seawarrior181/PasswordPump_II/3D-Print/Jimmys_Design/PXL_20210318_081315096.jpg

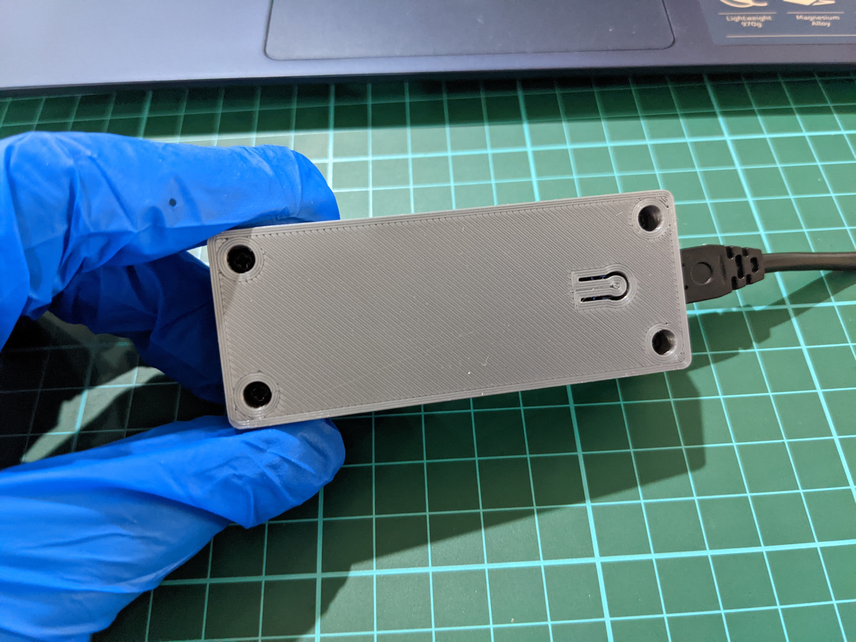
3D-Print/Jimmys_Design/PXL_20210318_081315096.jpg
