seawarrior181/PasswordPump_II/3D-Print/scootercommuter_Design/EncoderModel/PPBox_1.jpg

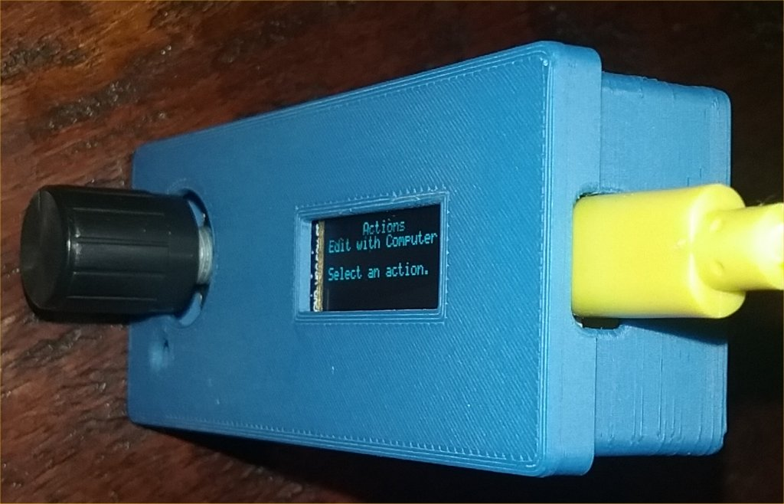
3D-Print/scootercommuter_Design/EncoderModel/PPBox_1.jpg
