seawarrior181/PasswordPump_II/3D-Print/scootercommuter_Design/EncoderModel/PPBox_2.jpg

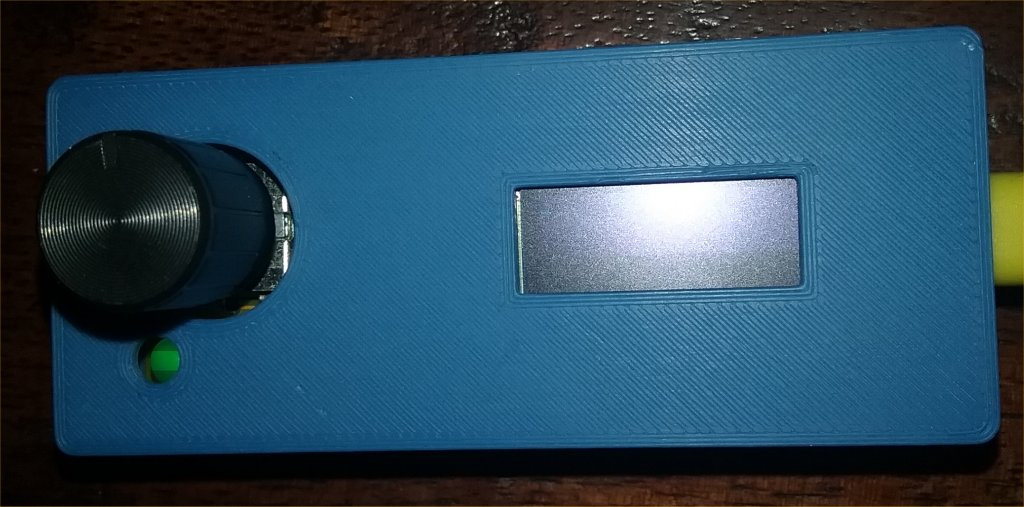
3D-Print/scootercommuter_Design/EncoderModel/PPBox_2.jpg
