seawarrior181/PasswordPump_II/media/20200301_110927.jpg

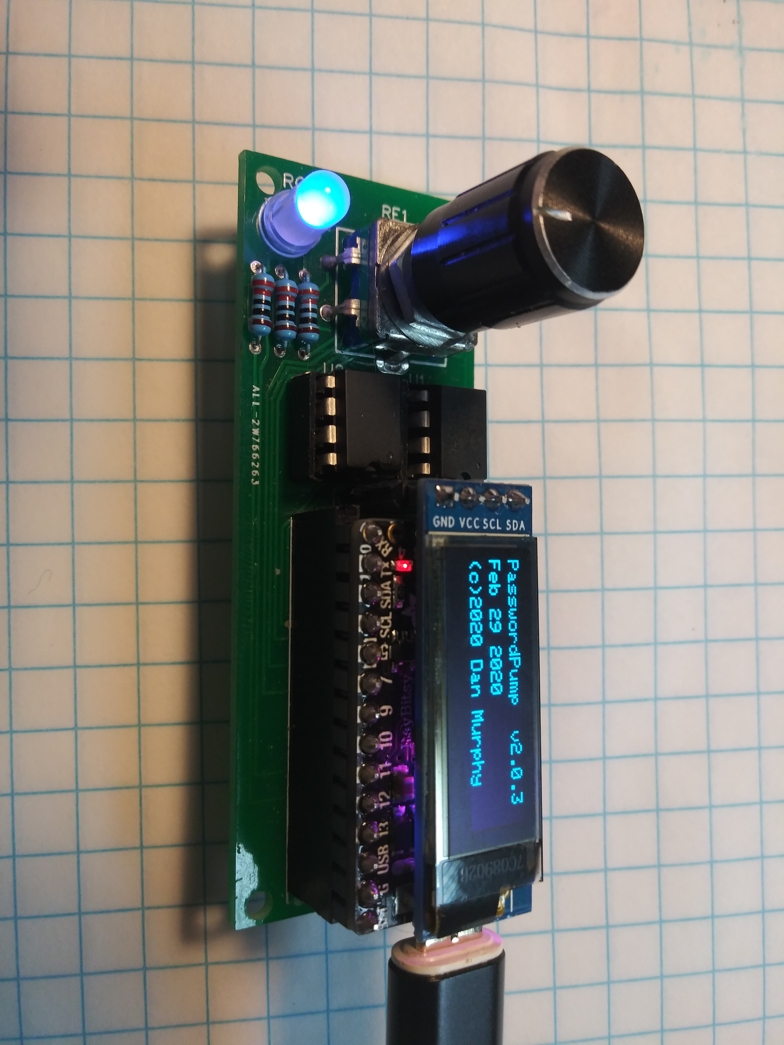
media/20200301_110927.jpg
