seawarrior181/PasswordPump_II/media/20200301_113238.jpg

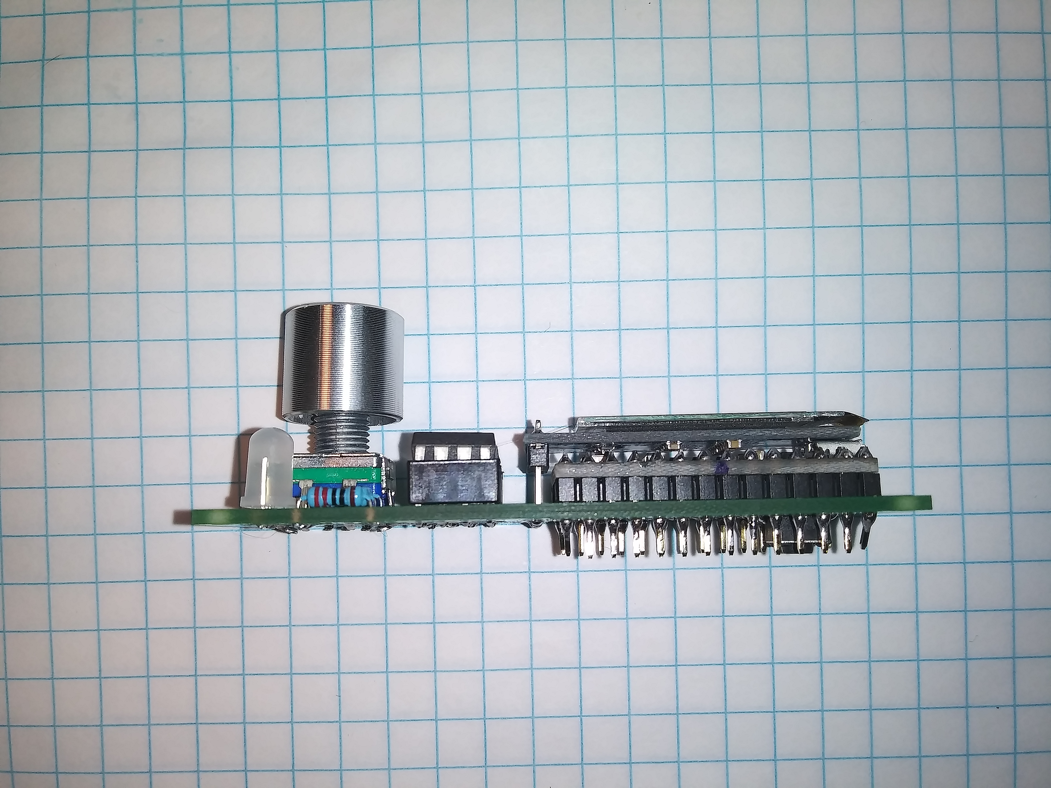
media/20200301_113238.jpg
