seawarrior181/PasswordPump_II/media/20200301_124309.jpg

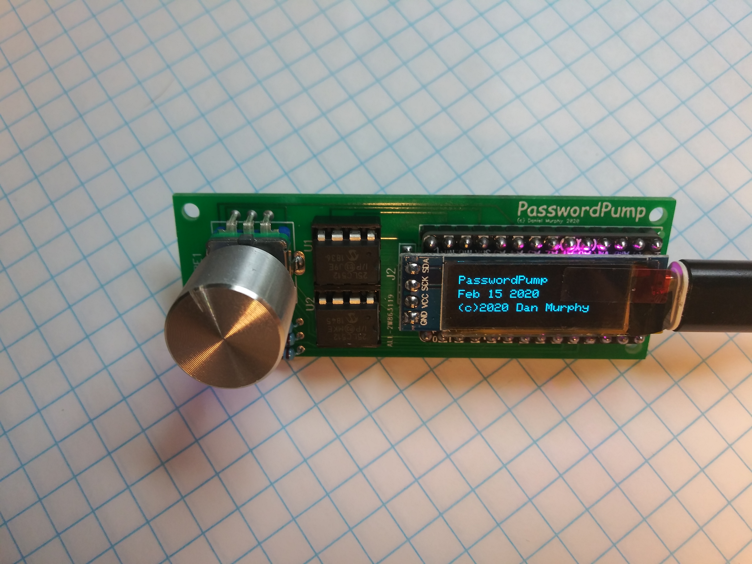
media/20200301_124309.jpg
