seawarrior181/PasswordPump_II/media/20200301_130727.jpg

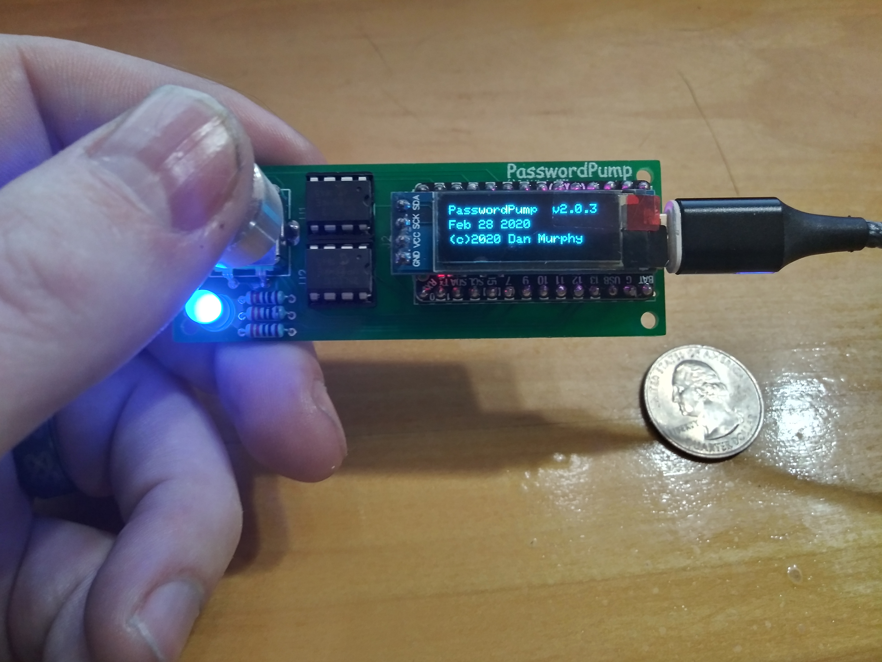
media/20200301_130727.jpg
