seawarrior181/PasswordPump_II/media/20201129_113634_HDR.jpg

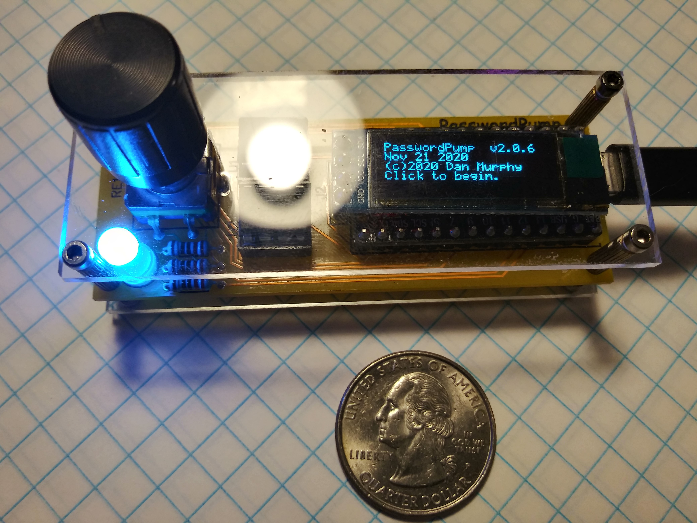
media/20201129_113634_HDR.jpg
