seawarrior181/PasswordPump_II/media/20210111_080319_HDR.jpg

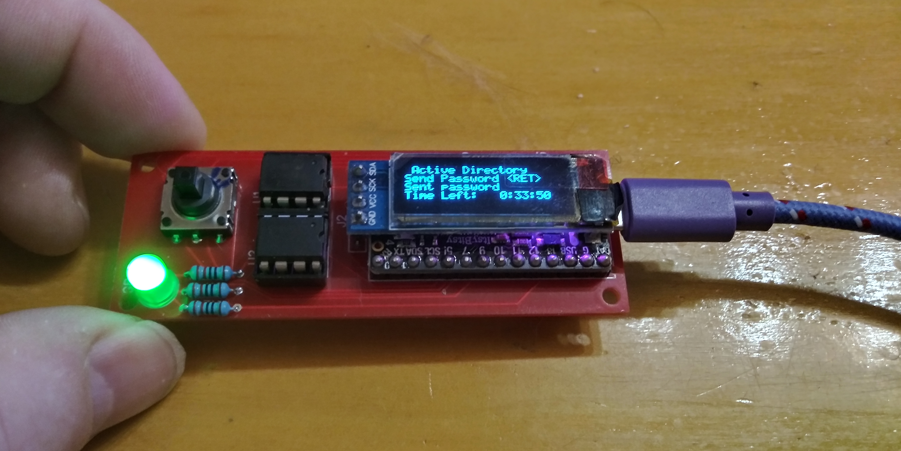
media/20210111_080319_HDR.jpg
