seawarrior181/PasswordPump_II/media/20210115_154211.jpg

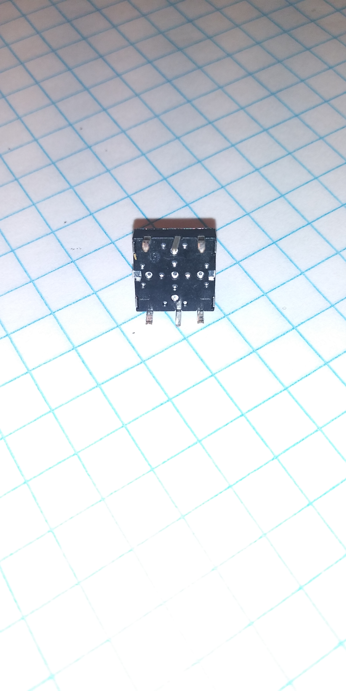
media/20210115_154211.jpg
