seawarrior181/PasswordPump_II/media/20210116_133526.jpg

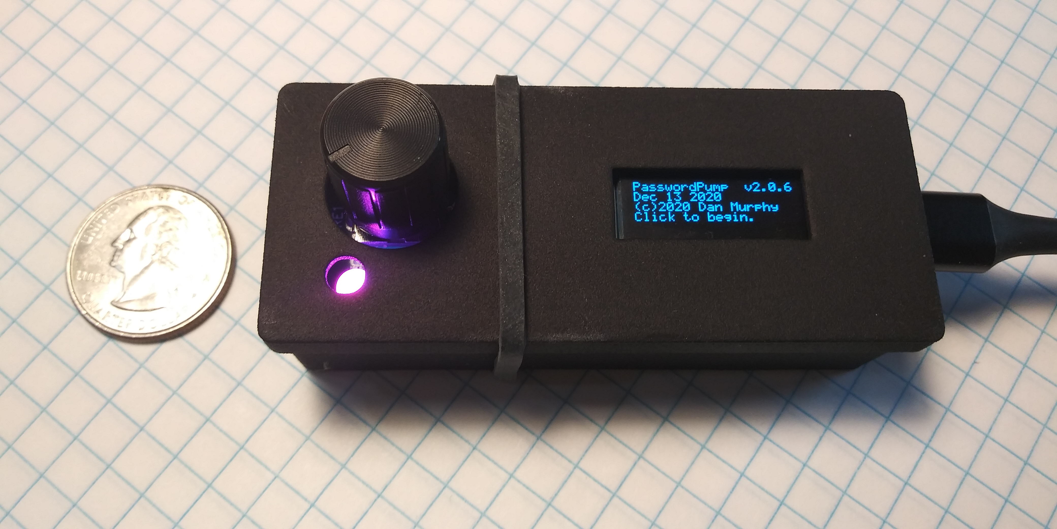
media/20210116_133526.jpg
