seawarrior181/PasswordPump_II/media/20210118_093656.jpg

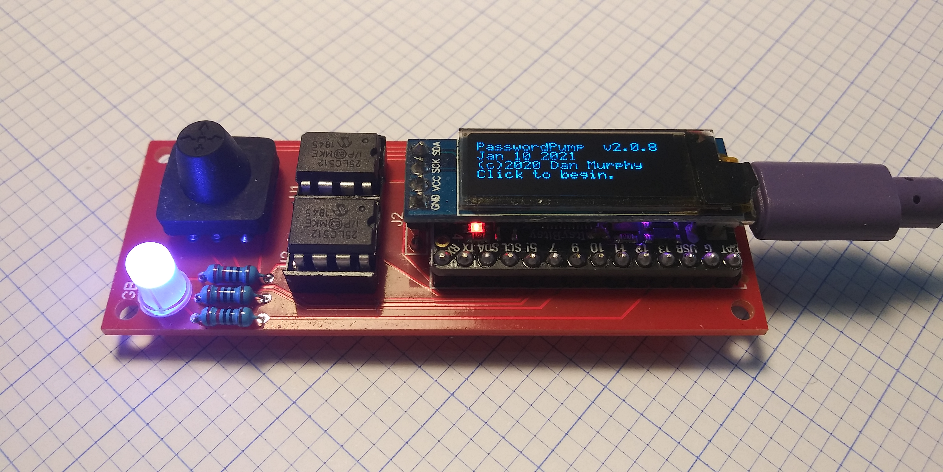
media/20210118_093656.jpg
