seawarrior181/PasswordPump_II/media/20210210_074406.jpg

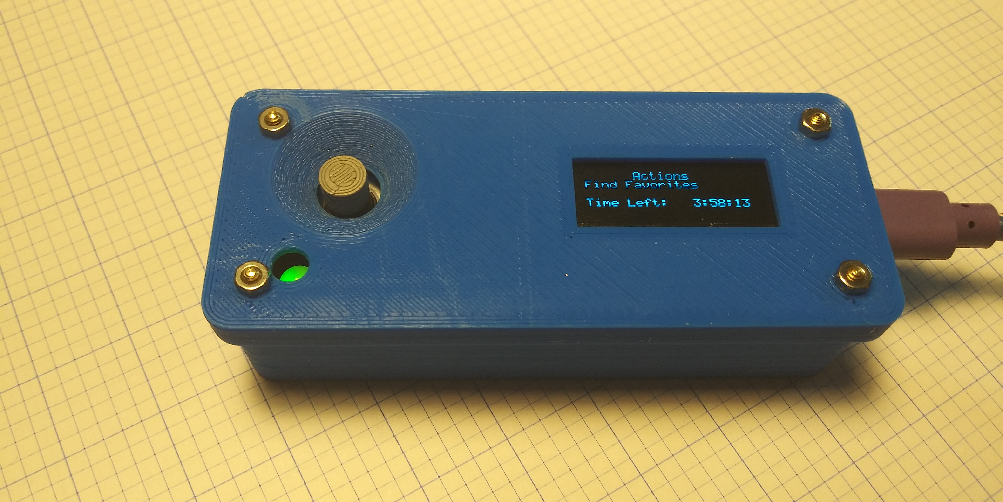
media/20210210_074406.jpg
