seawarrior181/PasswordPump_II/media/20210212_081341.jpg

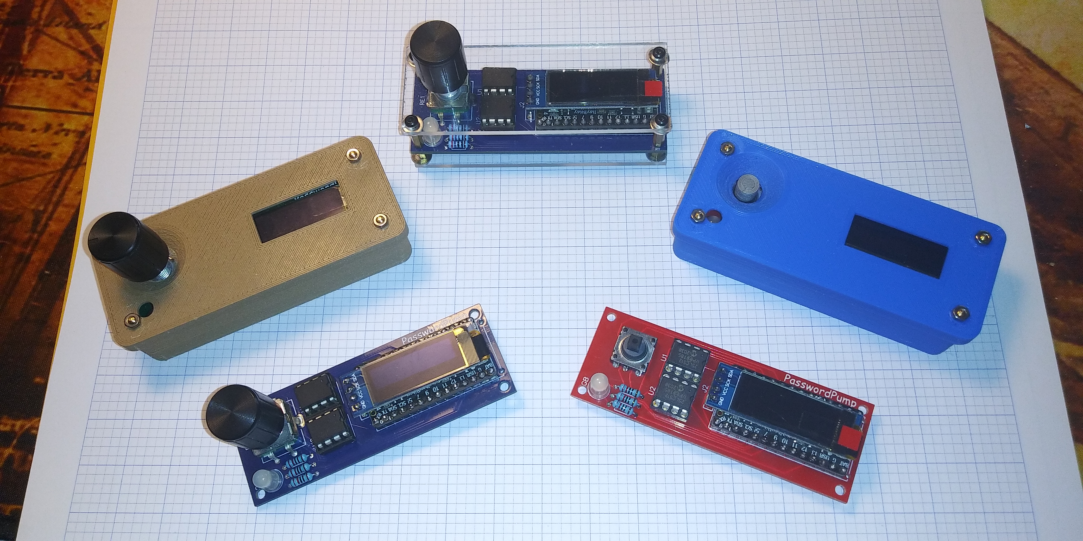
media/20210212_081341.jpg
