seawarrior181/PasswordPump_II/media/20210212_084028.jpg

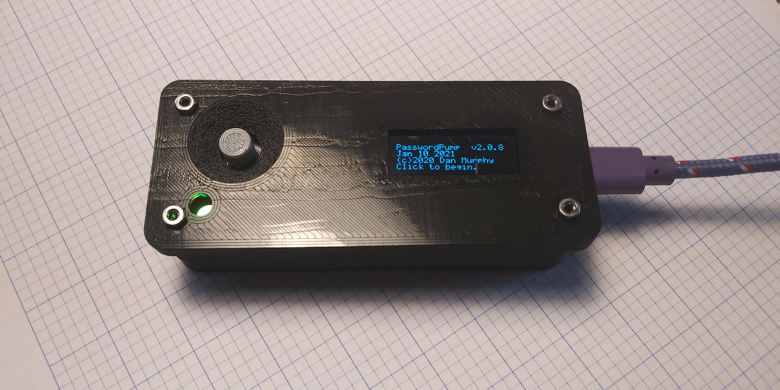
media/20210212_084028.jpg
