seawarrior181/PasswordPump_II/media/20210410_101105.jpg

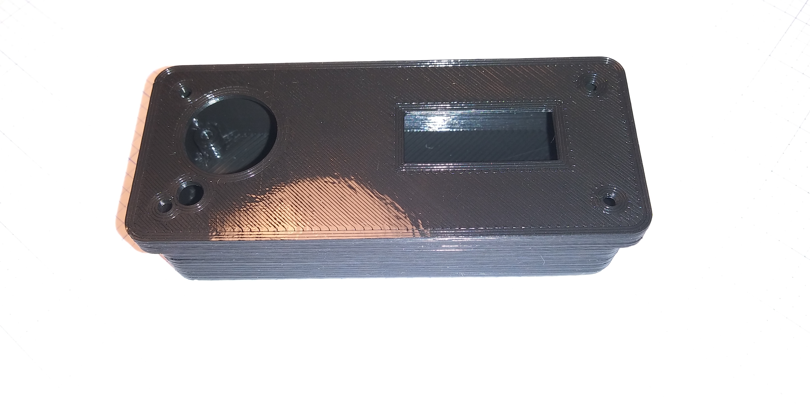
media/20210410_101105.jpg
