seawarrior181/PasswordPump_II/media/DriverUpdated.jpg

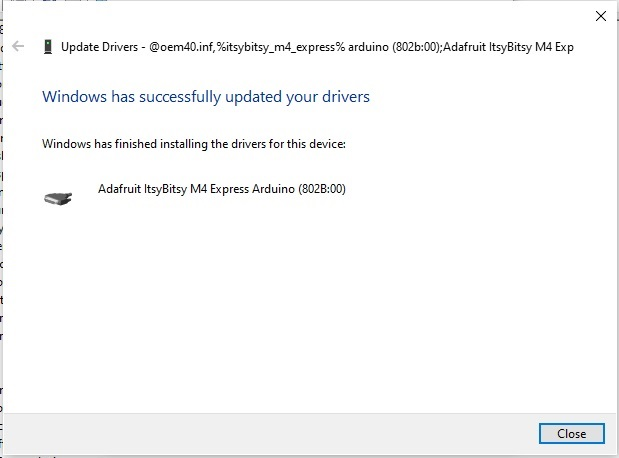
media/DriverUpdated.jpg
