seawarrior181/PasswordPump_II/media/DriverUpdated_2.jpg

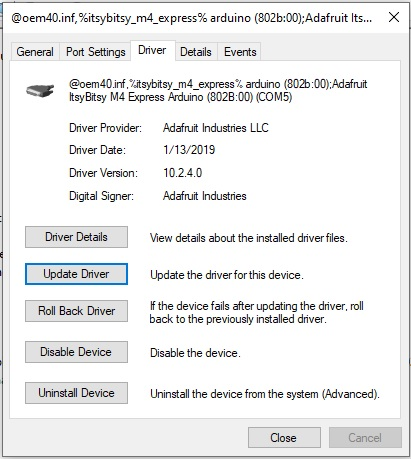
media/DriverUpdated_2.jpg
