seawarrior181/PasswordPump_II/media/FritzingBreadboard.jpg

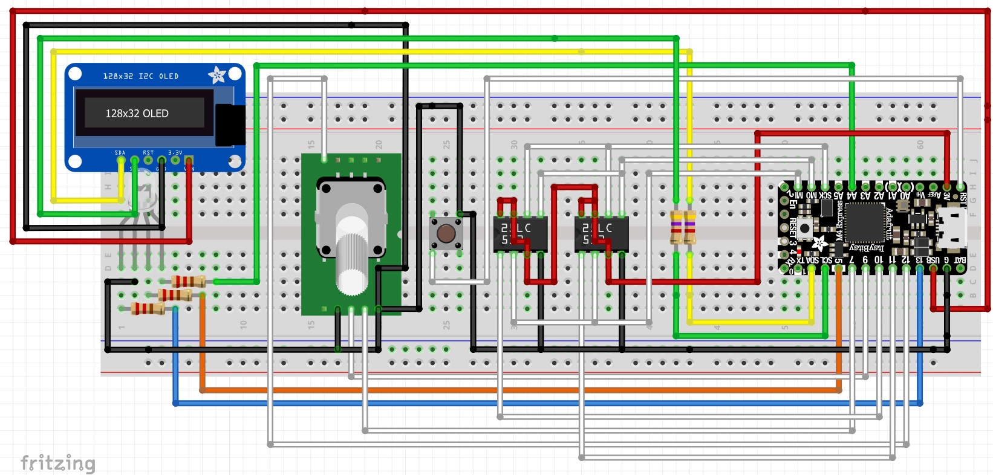
media/FritzingBreadboard.jpg
