seawarrior181/PasswordPump_II/media/JoystickGround.jpg

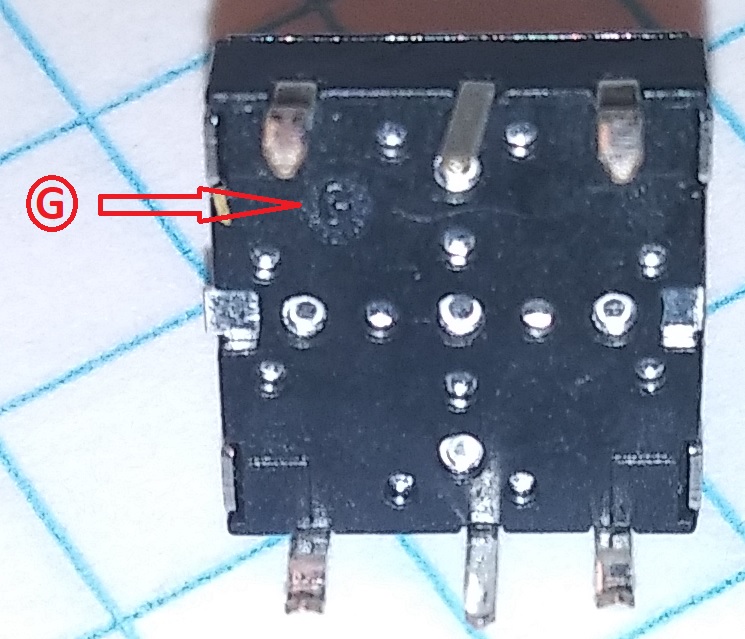
media/JoystickGround.jpg
