seawarrior181/PasswordPump_II/media/JoystickGroundLocation.jpg

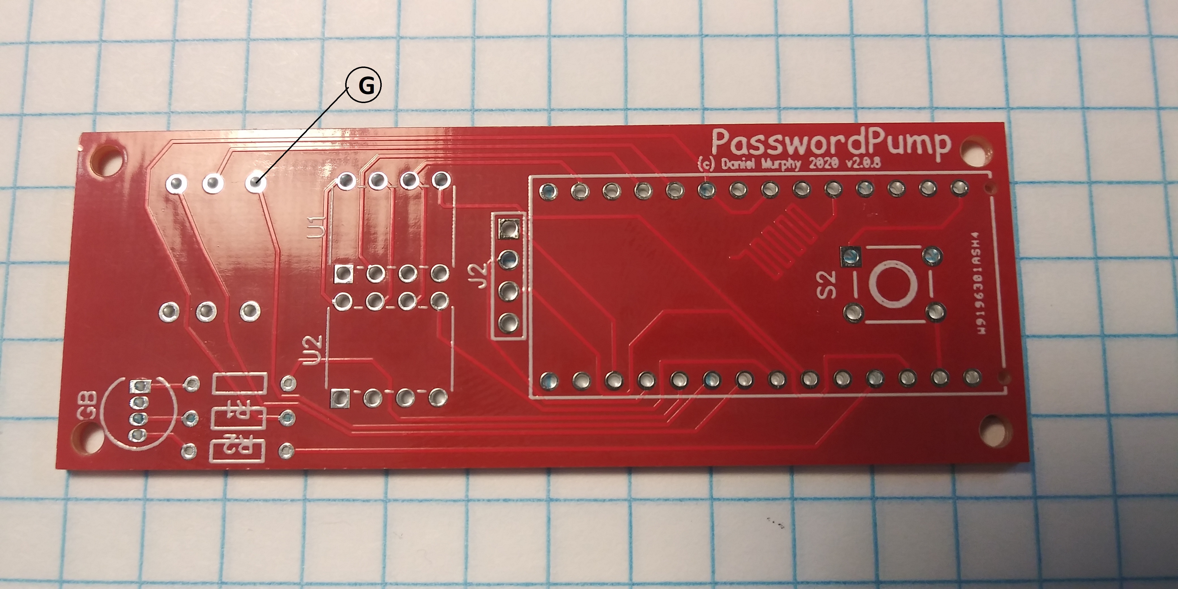
media/JoystickGroundLocation.jpg
