seawarrior181/PasswordPump_II/media/JoystickNubbin.jpg

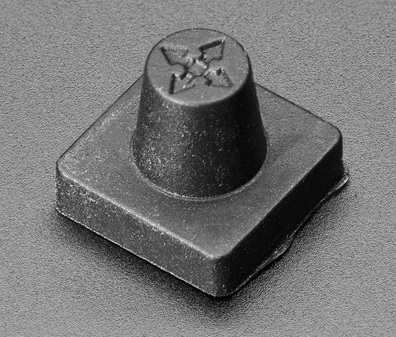
media/JoystickNubbin.jpg
