seawarrior181/PasswordPump_II/media/MaleHeaders.jpg

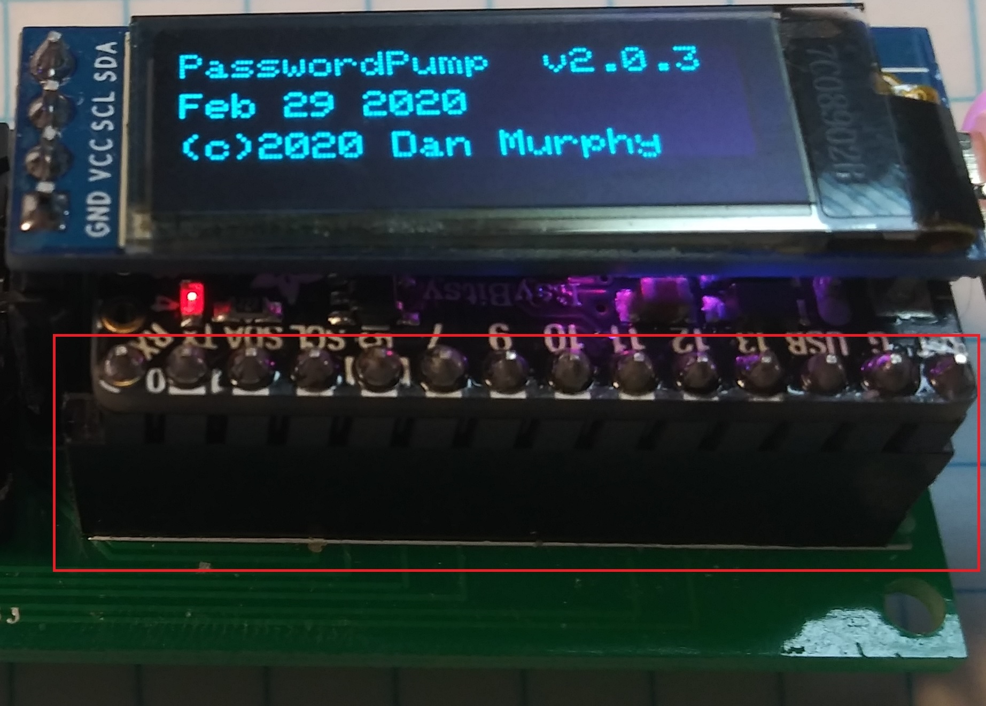
media/MaleHeaders.jpg
