seawarrior181/PasswordPump_II/media/Mods-1.jpg

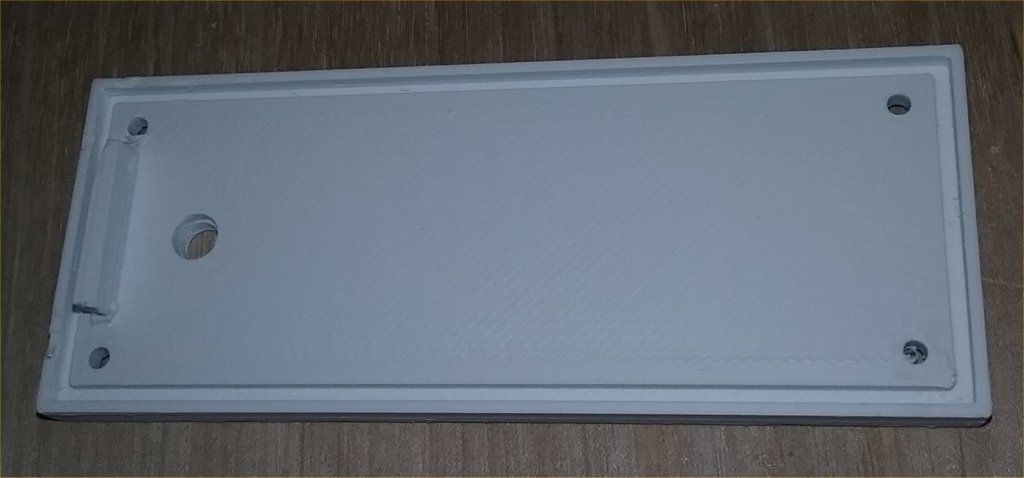
media/Mods-1.jpg
