seawarrior181/PasswordPump_II/media/Mods-2.jpg

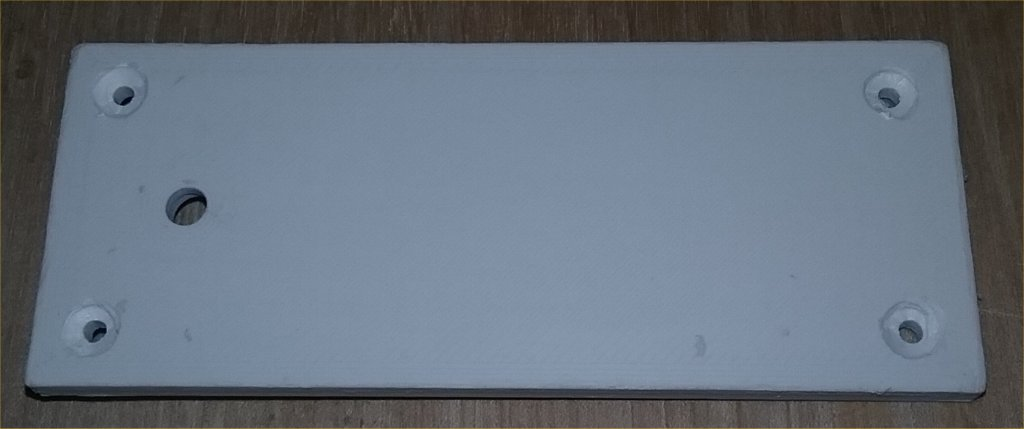
media/Mods-2.jpg
