seawarrior181/PasswordPump_II/media/Mods-4.jpg

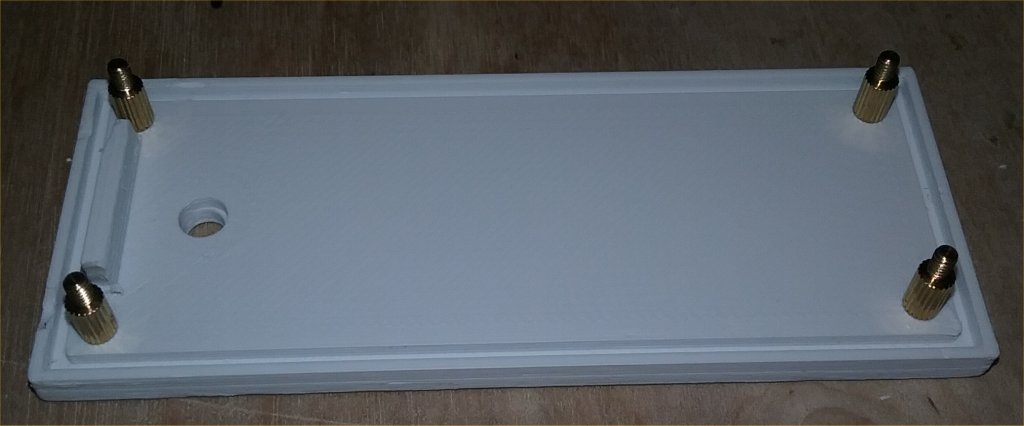
media/Mods-4.jpg
