seawarrior181/PasswordPump_II/media/Mods-5.jpg

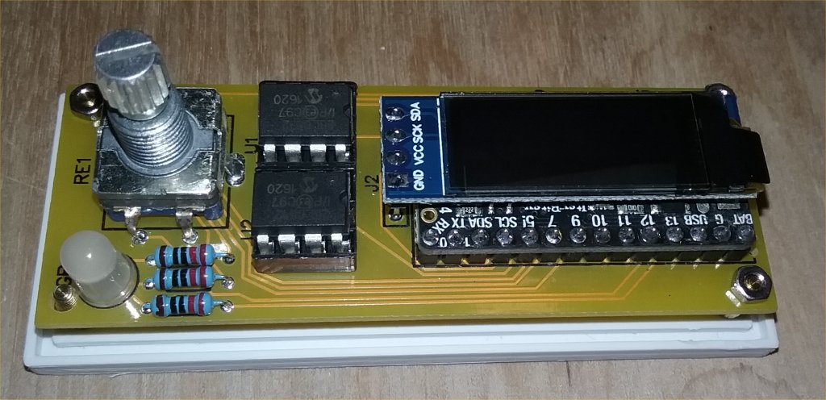
media/Mods-5.jpg
