seawarrior181/PasswordPump_II/media/Mods-6.jpg

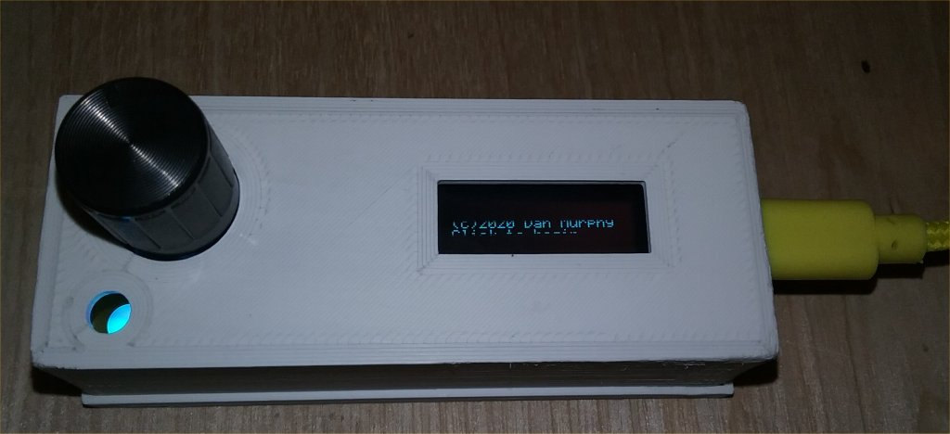
media/Mods-6.jpg
