seawarrior181/PasswordPump_II/media/PassPumpClient.gif

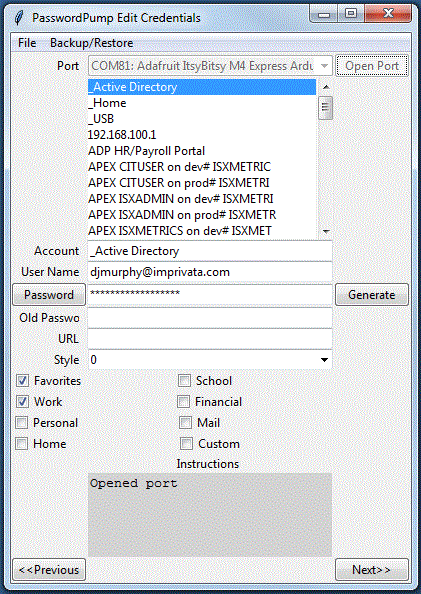
media/PassPumpClient.gif
