seawarrior181/PasswordPump_II/media/PasswordPumpGUI_2_4_0.jpg

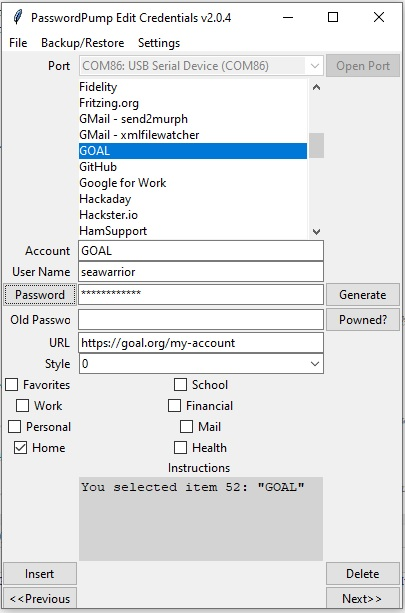
media/PasswordPumpGUI_2_4_0.jpg
