seawarrior181/PasswordPump_II/media/PasswordPumpGUI_v2_8_02_867.jpg

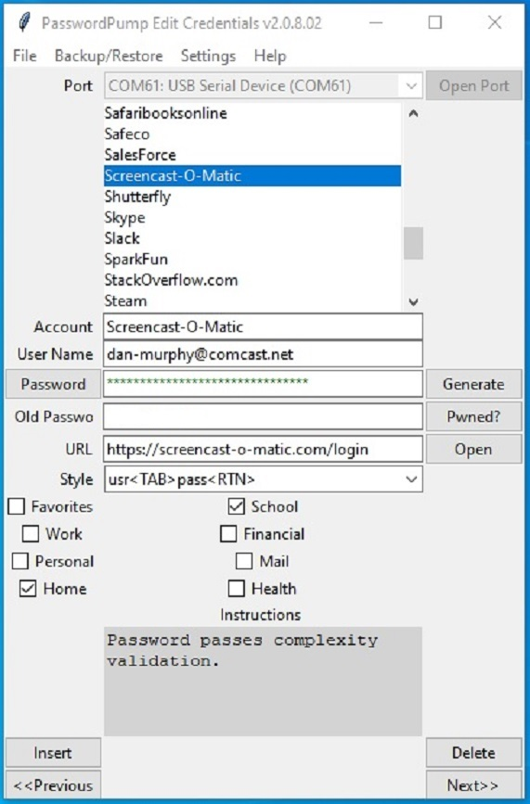
media/PasswordPumpGUI_v2_8_02_867.jpg
