seawarrior181/PasswordPump_II/media/PasswordPumpPCBBottom.jpg

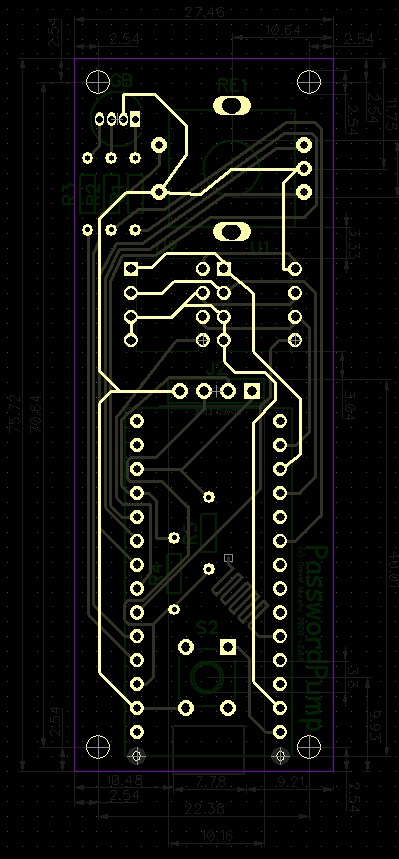
media/PasswordPumpPCBBottom.jpg
