seawarrior181/PasswordPump_II/media/PasswordPumpPCBJoystickTop_2_0_8.jpg

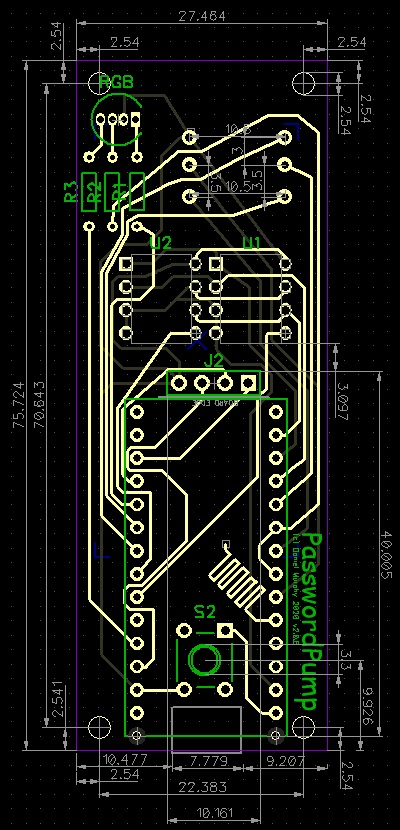
media/PasswordPumpPCBJoystickTop_2_0_8.jpg
