seawarrior181/PasswordPump_II/media/PasswordPumpPCBTop_2_0_4.jpg

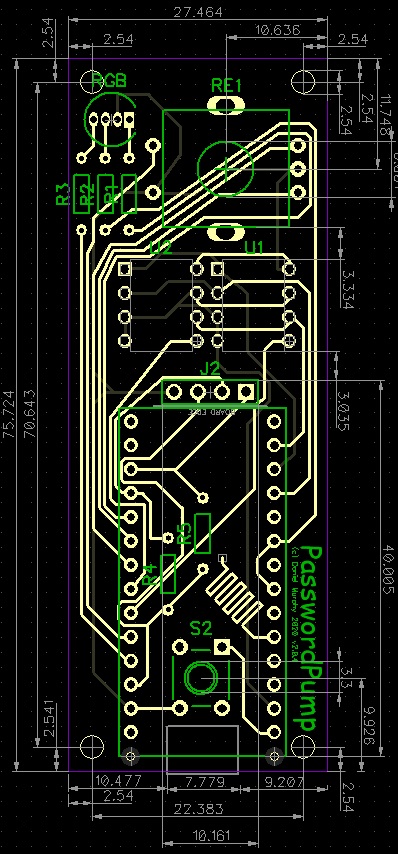
media/PasswordPumpPCBTop_2_0_4.jpg
