seawarrior181/PasswordPump_II/media/PPEncoder.jpg

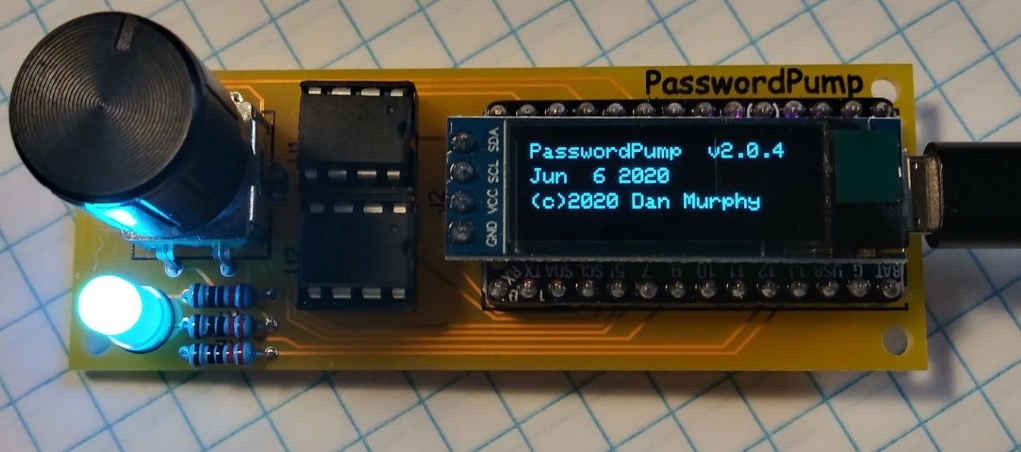
media/PPEncoder.jpg
