seawarrior181/PasswordPump_II/media/PPEncoderEnclosure.jpg

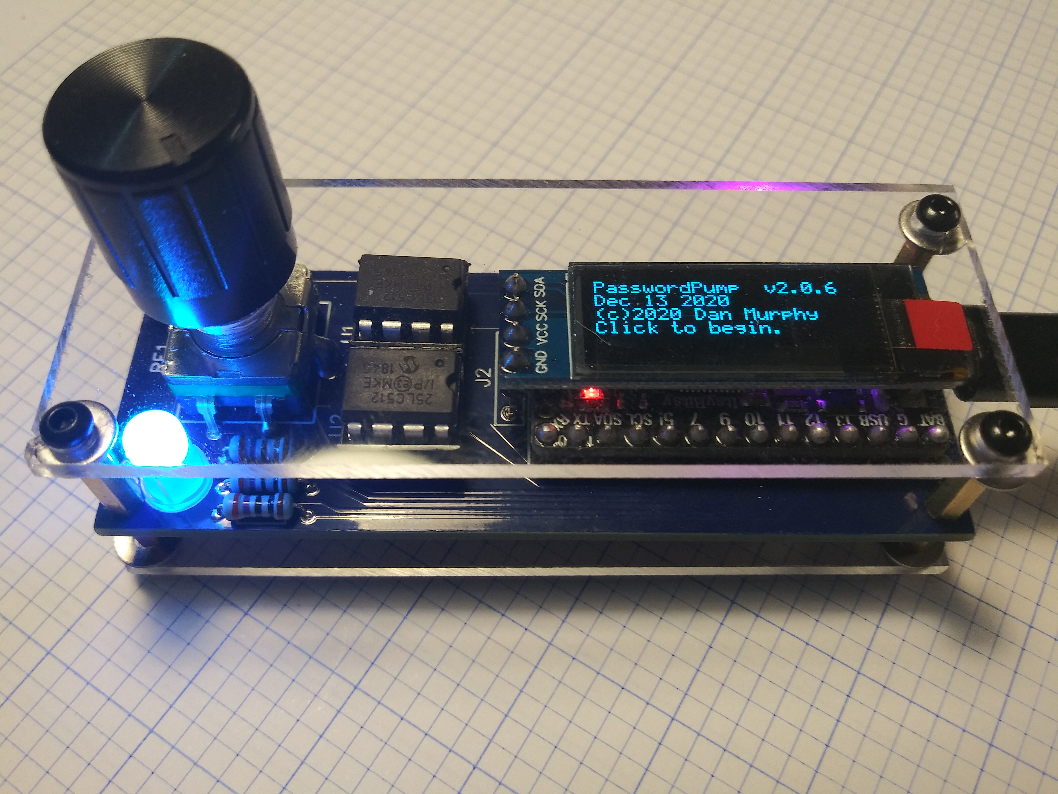
media/PPEncoderEnclosure.jpg
