seawarrior181/PasswordPump_II/media/PPJoystick.jpg

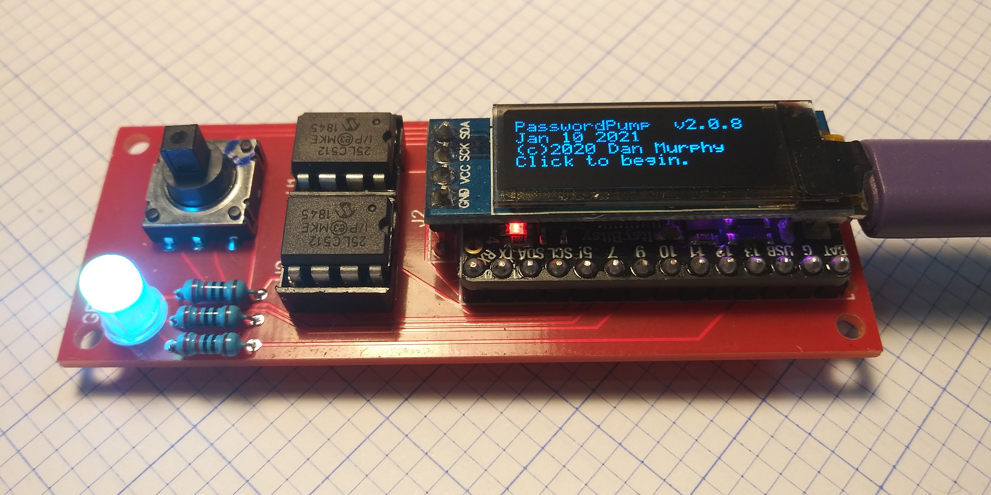
media/PPJoystick.jpg
