seawarrior181/PasswordPump_II/media/PPJoystickCase.jpg

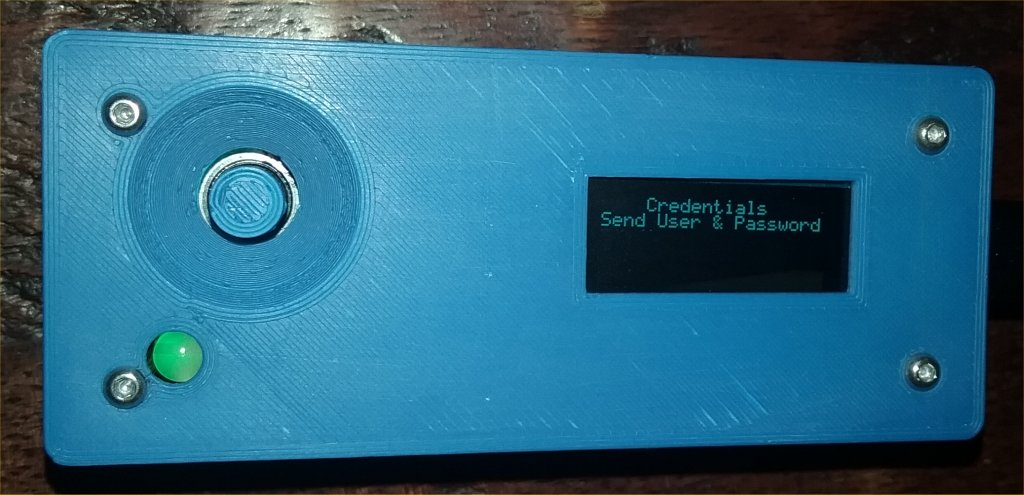
media/PPJoystickCase.jpg
