seawarrior181/PasswordPump_II/media/CircutPythonDeviceDriversInstalled.jpg

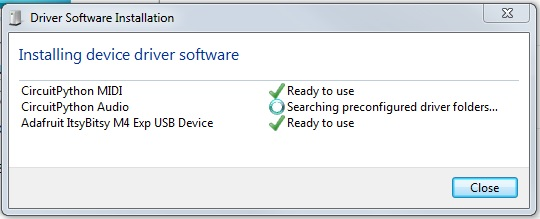
media/CircutPythonDeviceDriversInstalled.jpg
