seawarrior181/PasswordPump_II/v2_0_9/PasswordPump_v_2_0/PasswordPump_v_2_0.ino

/*               ___                              _ ___
                | _ \__ _ _______ __ _____ _ _ __| | _ \_  _ _ __  _ __ 
                |  _/ _` (_-<_-< V  V / _ \ '_/ _` |  _/ || | '  \| '_ \
                |_| \__,_/__/__/\_/\_/\___/_| \__,_|_|  \_,_|_|_|_| .__/
  Author:       Daniel J. Murphy                                  |_| 
  File:         PasswordPump_v_2_0.ino
  Version:      2.0.9.02
  Date:         2019/07/26 - 2023/03/21
  Language:     Arduino IDE 1.8.13, C++
  Device:       Adafruit ItsyBitsy  M0 Express‎ or Adafruit  ItsyBitsy M4 Express‎
  MCU:          ATSAMD21G18 32-bit  Cortex M0+  or  ATSAMD51J19 32-bit Cortex M4
  Memory:       256KB  Flash   and  32KB RAM   or  512KB  Flash  and   192KB RAM
  EEprom:       2MB of SPI Flash (not used)
  Clock Speed:  48 MHz (M0) or 120MHz (M4)
  Voltage:      3.3v MCU & 25LC512 EEProm / 5v RGB LED, Rotary Encoder,  SSD1306 
                OLED 
  Current:      0.03A
  Components:   RGB LED, SSD1306 128x32 LED  display, one momentary push button, 
                one  rotary encoder or one joystick,  3    220ohm      resistors  
                for  the  RGB  LED,  2 25LC512  external  EEprom  chips,  custom 
                PCB, 2 8 pin DIP holders, a  plastic  knob,  and  a  USB  cable.
  Purpose
  =======
  - To manage user names and passwords and to type them in to a computer, tablet 
    or phone via simulated USB keyboard.  To facilitate  the generation and  use 
    of extremely strong 31  character  UUID  like  passwords  on  all  accounts.
	
  Device Program Files
  ====================
  CzechKeyboard.h
  DanishKeyboard.h
  FinnishKeyboard.h
  FrenchKeyboard.h
  GermanKeyboard.h
  Keyboard.cpp
  Keyboard.h
  KeyboardTop.h
  NorwegianKeyboard.h
  PasswordPump_v_2_0.ino (this program)
  SpanishKeyboard.h
  SwedishKeyboard.h
  UKKeyboard.h
  USKeyboard.h
  
  Documentation
  =============
  For more information about this project visit 
  https://www.5volts.org/post/passwordpump-v2-0.
  To see the source code in GitHub point your browser to
  https://github.com/seawarrior181/PasswordPump_II.  
  To purchase a kit visit
  https://www.tindie.com/products/passwordpump/passwordpump-v20/
  To see a video about the project navigate to 
  https://www.youtube.com/watch?v=f4Iukt5VDUo.

  Features
  ========
  - Authenticate to device with up to a 16 character master password
  - Search for accounts
  - Send user name and password to computer phone or tablet as if typed in via 
    keyboard
  - Add account name, user name, password (generated or not), url, old 
    password
  - Edit existing user name, password, old password, groups/categories, URL, 
    style (inter-username/password character, <Return> or <Tab>)
  - Delete account
  - Generate password
  - Store old password
  - Data entry via rotary encoder or keyboard and serial monitor, or via client
    Python program running in Windows, Mac or Linux.
  - Accounts added in alphabetical order
  - Store up to 253 sets of credentials
  - Backup all accounts to a second encrypted external EEprom
  - Logout / de-authenticate / lock computer (Windows only) via menu
  - Factory reset via menu (when authenticated)
  - Configurable password display on or off
  - Configurable failed login count factory reset (3, 5, 10, 25)
  - Configurable automatic logout after count of minutes (30, 60, 90, 120, 240,
    1, Never)
  - When automatic logout set to Never, screen times out in 5 minutes to avoid
    screen burn-in.
  - Configurable RGB LED intensity (high, medium, low, off)
  - Configurable font
  - Configurable display orientation (rotary encoder on the left or the right)
  - Configurable generated password size; 8, 10, 16, 24 or 31.
  - All passwords (except master password) are encrypted w/ AES-256; master 
    password is hashed w/ SHA-256.
  - Change master password
  - Export/Import to/from PasswordPump CSV format; encrypt exported file 
  - Import KeePass exported CSV file
  - Import passwords from Chrome
  - Associate credentials with custom groups for better organization; search by 
    group. Defaults are (Favorites, Work, Personal, Home, School, Financial, 
    Mail, Custom)
  - Decoy password feature that automatically factory resets the device if
    entered (e.g. while the user is under duress)
  - Supports use of several international keyboards.
  - Check if password is pwned/appeard in a data breach (in Python GUI)
  - Check for password complexity (in Python GUI only)
  
  Compatability
  =============
  The PasswordPump has been shown to work with Windows and Linux machines, 
  Apple, and Android phones and tablets.  Specifically the following are 
  supported:
   - Windows 7, 10, 11
   - Mac OS X
   - Ubuntu
   - Raspberry Pi OS (Raspbian)
   - Android
  If you’ve successfully (or unsuccessfully) used the PasswordPump with an 
  operating system that’s not on this list let me know so I can add it.
  
  Known Defects/Issues
  ====================  
    - = outstanding             
		! = will not fix
    x = fixed but needs testing 
    * = fixed - if a release is listed, that's the release in which it was fixed                  

 1- The linked list that manages the list of accounts is sometimes corrupted. 
    To mitigate this I added a 'Fix Corruption' feature that should address any 
    corruption in the linked list. Exact conditions of corruption cannot be 
    reproduced in the lab at this time, and code changes have been made in an 
    attepmt to fix it. This issue has been reported by one customer.
 2- Embedded quote in a CSV import file are not getting saved to the file e.g.
    password.
 3- When you import credentials with <CR><LF> in the account name bad things
    happen.
  - A user has reported then when selecting the Decoy Password setting the 
    device freezes.  Cannot reproduce in lab.

  ! If you've set the keyboard language during a session, then you select
    factory reset, the keyboard language is not reset to the default until you 
    press the reset button.
  ! When entering an account name 29 chars long via keyboard, nothing gets 
    entered.  I doubt that anyone is actually entering credentials via
    serial terminal at this point.  Use PasswordPumpGUI instead.
  ! In the switch statement for EVENT_SINGLE_CLICK the case statements 
    are not in order. When they are in order it doesn't evaluate 
    correctly.
  ! Fix the inconsistency with the on-board RGB LED and the 5mm Diff RGB LED.

  x Duplicate names freeze the MCU in the keepass import file (consecutive?)

  * When interacting with the PasswordPumpGUI during group customization the
    PasswordPump gets confused and group names are corrupted.
  * When using the PasswordPump with some tablets and phones the input from the
    PasswordPump seems too fast because characters are dropped.  Add the ability
    to slow down the input from the PasswordPump to the target device.
  * When changing orientation the joystick doesn't adjust correctly.
  * Single character user names and passwords are not working well
  * When deleting the first account in the linked list and then running fix
    corruption, it would have the effect of deleting all accounts (corrupted
    the linked list).
  * After a Factory Reset operation, the encoder type, font, and orientation
    settings were persisting until a hard reset was performed.
  * You can only select a new keyboard language once, the second time will 
    freeze the MCU.  To work around this resetting the keyboard more than
    once is prohibited. If you do reset the keyboard a second time you need
    to reset the device for the change to take effect.
  * Enabled the ability to fix a corrupt linked account list.
  * Delete screws up the account count when it leaves a hole.  e.g. add AAA, 
    BBB, CCC; delete BBB, you'll only be able to "Find" AAA.
  * Does not work correctly with keyboards that are not US.
	* Issue because listHead is set to 0 before there are any elements in the 
	  linked list; after factory reset when importing credentials ERR: 031
		appears, but it's benign.
  * It is possible to enter a duplicate account via the PasswordPump device.
  * When deleting duplicate accounts (duplicate account names) corruption is 
    introduced.
  * Decoy password feature is not working when the decoy password is entered.
	* 2.4.0: Via PasswordPumpGUI Insert, then <Alt><Tab> to another application.  
		Upon returning to PasswordPumpGUI the Account Name is "Unknown".  Set focus
		to another account, the PasswordPump and PasswordPumpGUI freeze.  Close the
		PasswordPumpGUI window and long click on the PasswordPump.  Now there is
		only one account in the PasswordPump. Restore from secondary EEprom.
  * Single click after Reset brings you to alpha edit mode
  * Should probably remove Keyboard ON/OFF from saved properties and always 
    default to Keyboard OFF; or make sure it is always OFF when backing up 
    EEProm.
  * Added account 'Add Account' and then deleted, corrupted linked list
  * Added account to the end of the linked list, corrupted linked list
  * After deleting account change the location of the menu
  * Nail down the menu / UI layout.  
  * Navigation back to previous menu needs work (EVENT_LONG_CLICK).
  * When returning from setting anthing in the settings menu you're not returned
    to the menu item from where you came.
  * When long clicking after search by group you don't return to the right 
    group you always return to favorites.
  * The automatic logout of the PasswordPump after inactivity is also locking
    the computer.  It should just logout of the PasswordPump.
  * User can scroll past z when entering text.
  * If you add an account via PasswordPumpGUI and never visit the URL field,
    garbage is shown for the URL via the PasswordPump UI.
  * When doing a master password change one of the accounts always ends up 
    corrupt.
  * Old password is getting populated with junk in unknown circumstances
  * If there are commas or double quotes in the text of a field we're trying to
    import, import breaks.
  * When a user name isn't specified in a KeePass export file, the password 
    isn't populated at all (it's blank).(no longer relevant)
  * Some character loss when exporting to PPEXPORT.CSV and then re-importing.
    (no longer relevant)
  * Fix defect in FindAccountPos; ERR: 033 when importing existing account
    (intermittent) (no longer relevant)
  * See if you can change the font of the UI and add a fourth line. (can't)
  * we are only encrypting the first 16 characters of account name, user name 
    and password.  The sha256 block size is 16.
  * A forward slash (escape character) at the end of a field causes the PC UI
    to throw an exception.
  * When there is a tilde (~) in a field this causes the PC UI to throw an 
    exception.
  * We are only accommodating password length of 30 instead of 31 when 
    interacting with the PasswordPumpGUI.  Same problem with user names.
  * See if you can add one more char to the horizontal size of the SSD1306. (No)
  * It's not possible to add a new account via the PC client.
  * When adding an account via rotary encoder it's automatically assigned to the
    favorites group.
  * You can import 51 accounts, and exit from the python UI, and then navigate
    through the accounts on the device, but if you power cycle the device all of
    the accounts disappear.
  * PC client isn't working correctly, the fields are not getting enabled.
  * URLs exceeding ABOUT 53 characters are not importing correctly.
  * Add Web Site to the python client and test.
  * Entering Find Favorites when there are no Favorites yields undefined 
    behavior.
  * Can't seem to send a <tab> character via the Keyboard.  Tried KEY_TAB, 
    TAB_KEY, 0x2b, 0xB3, '  '.
  * Find Favorites freezes the MCU if there are no favorites (or shows garbage)
  * The problem with the rotary encoder needs to be addressed.
  * When updating an existing account via import KeePass, the linked list is
    corrupted even though the account name isn't changed.  Go from 111 accounts
    to 93 accounts when update Wachusette.
  * Overflow probably causes automatic logout even when logoutTimeout is set to 
    0
  * When you put in a master password longer than the real master password
    authentication succeeds. [CAN'T REPRODUCE]
  * make the display 20 characters wide
  * There should be another option in Send Credentials, an option to send the 
    password with and without the <RET> at the end.
  * Test w/ 25LC512 chips.
  * Setup of the keyboard and show passwords menu items is freezing the mcu.
  * URLs over 64 characters were not loading because of the EEProm page size.
  * Change master password results in encrypted account creds displaying
  * The default inter credentials character should be <TAB>.
  * There doesn't seem to be a delay anymore between the sending of the account 
    name and the sending of the password.
  * The first and last sets of credentials imported appear encrypted to the 
    user.
  * Consider removing "&" from the legal characters when a password/UUID is 
    generated.
  * An account name that exceeded 31 chars imported in entirety, wasn't 
    truncated at 31 chars.  APEX... [burned by Notepad++ again]
  * RGB LED is too bright.
  * After entering Style, we return to Account Name, but account name is blank.
  * When importing 112 keepass credential sets only 49 make it into the EEprom.
  * remove inclusion of /\@"'` from generated passwords
  * we are authenticated after blowing all the credentials away after 10 
    failures
  * Phantom account is getting added to the list of accounts
  * Fix issue w/ screen "trash"
  * DisplayLine2 needs to be blanked out after retuning from Find or Add acct.
  * When you enter Find Account the account name of the first account isn't 
    getting displayed (except on display line 3).
  * FactoryReset isn't deleting credentials
  * after deleting an account we're returned to the send credentials menu 
    instead of the find account menu
  * When logging in via Remote Desktop and suppling the user name and password,
    we seem to 'hit return' after entering just the user name.
  * automatic initialization after 10 failed login attempts is prompting the 
    user to confirm the action.
  * When you select add account and immediately scroll through the options there
    is apparent corruption in the menu selections
  * Long clicking out of confirm account delete brings you to the main menu 
    instead of the edit credentials menu.
  * When we first enter the find account menu the currentAccount can be wrong
  * don't show Master Password menu choice after authenticating
  * Deleting the head or tail results in corruption
  * When using extended memory crash at line 1367 where the LCD output is 
    trashed. Suspect some conflict w/ the 25LC256 EEprom chip.  Hangs subsequent
    to line 1367. Search for "trashed".
  * Backup All to a file isn't in alphabetical order
  * Backup all isn't consistently printing carriage returns.
  * passwords are not generating correctly
  * the LCD's back-light is not turning on, needed to operate in the dark
  * after add account the account isn't showing in find account
  * after hitting reset show password = 0
  * turning the rotary encoder fast doesn't scroll through the menu fast  
    [sending output to the serial monitor corrects this] 
  * can't add a new account; can't scroll edit menu on first account add
  * long click seems too long
  * first account added doesn't immediately show in find account after it's 
    added.
  * after reset, stuck in reset.
  * in LCD mode too many chars in "Show Passwrd OFF", freezes device.
  * Crash when scrolling up the menu after selecting 'add account'.
  * failures are not showing correctly because you need to blank out the line 
    first
  * after adding an account we can't find it
  
  TODO / Enhancements
  ===================
    - = unimplemented
    ? = tried to implement, ran into problems
    % = concerned there isn't enough memory left to implement
    ! = will not implement
    x = implemented but not tested  
    * = implemented and tested

  - In general, vastly improve the international keyboard support.
  - On Linux machine you have to press "GUI key + Escape" to log out, rather 
    than "GUI key + L" as on Windows. Logout and lock feature should be able to 
    logout of a Linux machine.
  - Somehow signal to the user when entering the master password for the first 
    time.
  - Add the ability to pump a single tab or a single carriage return from the 
    menu.
  - Import KeePass .xml file
  - Import LastPass files
  - Export to KeePass CSV format
  - Export to LastPass format
  - re-enter master password to authorize credentials reset
  - Consolidate code in the import files sections (this code is currently 
	  commented out.
  - A back space should be available during character input via rotary encoder.
  - Implement more error codes
  - Scroll the display horizontally when necessary
  - Make the menus scroll around when the end is reached (?)
  - Add Italian keyboard support: 
    https://github.com/Maiux92/digispark-keyboard-layout-italian/blob/master/scancode-ascii-table.h

  ! Make it work over bluetooth
  ! Make UN_PW_DELAY configurable
  ! Confirm that the lock bits are correctly set.

  ? Add a feature whereby the unit factory resets after two triple clicks, even
    if not yet authenticated. (commented out, caused problems)
  ? Add a feature whereby the unit logs out after two double clicks. (commented
    out, caused problems)

  * Create an excellent case or enclosure.
  * Make the size of the generated password configurable.
  * Implement a password complexity check for generated passwords that matches
    the complexity of passwords generated via PasswordPumpGUI.  It's currently
    possible to generate a password on the device that doesn't pass complexity
    rules.
	* In the customize groups menu, use the current name of the group instead of
	  the group number.
  * Add the ability to fix a corrupt linked list.
  * Add a decoy password that executes a factory reset when the password plus
    the characters "FR" are supplied as the master password.
  * Enable decoy password feature, make it configurable
  * Allow users to name the categories.
  * Dim the display when it's not in use.
  * Always reflect the account that's selected in the PC client on the device.
  * Automatic logout countdown
  * Increase the display width by 1 more (tried and this didn't work)
  * Add salt for credentials, char UUID
  * Add ability to save the old password, especially useful if a generated 
    password is rejected when changing passwords
  * Make saving of previous password manual
  * add salt to the hashed master password.
  * ensure we don't read more bytes than that which we can accommodate in the
    buffer
  * encrypt the user names (need to confirm by examining EEprom)
  * encrypt the account names (need to confirm by examining EEprom)
  * Configure how long until automatic logout
  * Try updating write_eeprom_array() so that it's not writing byte for byte 
    to improve write speed.
  * Replace AES-128 with AES-256
  * Build a Windows client (in python) for editing credentials; 
    add/change/delete
  * Add website to the Python client
  * Add an Import menu
  * Change master password (use both 25LC256 chips for this)
  * Backup to file should backup to a format that can be read in, and should 
    include the groups.
  * Add a menu for selecting the number of failed logins before reset (will this
    make it easier to hack into the device?)
  * Add a setting to indicate how many failed login attempts before factory 
    reset.
  * Remove the EEprom part number selection menu.
  * Document how to burn the firmware outside of the Arduino IDE
  * Set all unused I/O pins as output, not connected to a resistor and best to 
    set to zero logic low
  * Accommodate a larger EEProm chip (512)
  * Import Chrome passwords
  * Import PasswordPump .CSV file
  * Increase the website size to at least 96.
  * Mark favorite credentials, and Find Favorites menu item
  * Add website url to credentials
  * Add a favorites designator to sets of credentials, and a menu item that lets
    you Find Favorites only; it should be the default / top of the Main menu.
  * Flash the RGB when there are 10 seconds remaining until logout
  * Erase the KeePass import file by filling it w/ null terminator and then 
    deleting it.
  * Make style indicator more intelligent e.g. <RETURN> or <TAB>
  * Consider halving the number of possible accounts (from 256 to 128) and 
    doubling the size of the account name, usern ame, and password fields (from
    31 to 63).
  * Turn off the RGB LED, configurable
  * Make brightness of RGB LED configurable (use PWM)
  * Add the ability to send the URL through the keyboard
  * Add a new Settings menu selection
  * Add a missing pull up resistor for I2C to SSD1306 (bread board only)
  * implement with a better font
  * work on the work-flow; which menu items are defaulted after which events.
  * Delete account (account name, user name, password)
  * substitute memcpy with for loops
  * implement a doubly linked list to keep the accounts in order
  * reconsider the organization of the menus
  * ask for confirmation before performing destructive tasks
  * Restore backup (restore from the EEprom backup)
  * implement backup from external EEprom to external EEprom
  * incorporate the use of external EEprom chip to expand available memory
  * make it possible to edit credentials via keyboard
  * Encrypt all passwords (except the master password)
  * finish the video
    https://screencast-o-matic.com/
  * decide if the encrypted password will be saved to EEprom
  * get ScreenCastOMatic to record the video for the project
  * add function(s) to send error output to the display device (e.g. no external
    EEprom.
  * Make it possible to send the account name, where a URL can be entered.
  * eliminate the need for the acctsArray to conserve memory.
  * make room for a next pointer and a previous pointer to maintain a doubly 
    linked list so that we can sort the account names.
  * decide if you should display the passwords.  Possibly make it configurable.
  * mask passwords on input
  * add a feature that dumps all account names, user names and passwords out
    through the keyboard (like to be inserted into an editor as a backup).
  * have the unit factory reset after 10 failed attempts.  Store the failed
    attempts in EEprom.
  * Hash the master password
  * A master key generated from the user password is hashed using SHA-256, which 
    is subsequently used to encrypt the password database with AES-128. 
    Cryptography experts no longer recommend CBC for use in newer designs. It 
    was an important mode in the past but newer designs should be using 
    authenticated encryption with associated data (AEAD) instead.   
  * have the unit automatically logout after a period of inactivity, this will
    require use of the timer.
  * After 5 minutes of inactivity clear the screen if the logout timeout is set
    set to Never (0).  Implemented 2023-03-18.

  Warnings
  ========
  - Avoid using the device with wet hands unless you have a case or enclosure.
  
  Suggestions
  ===========
  - Best viewed in an editor w/ 160 columns, most comments start at column 81 
  - Please submit defects you find so I can improve the quality of the program
    and learn more about embedded programming.  dan-murphy@comcast.net
  - For anyone unfamiliar w/ Arduino when the device is powered on first setup() 
    runs and then loop() runs, in a loop, in perpetuity.
  - Set tab spacing to 2 space characters in your editor.
	- Uncomment the pre-compiler directive __SAMD21__	if you're using the 
	  Adafruit ItsyBitsy M0, and comment out the pre-compiler directive 
		__SAMD51__.  Uncomment the pre-compiler directive __SAMD51__ if you're
		using the Adafruit ItsyBitsy M4, and comment out the pre-compiler directive
		__SAMD21__.  Set the precompiler directive (MODEL) for encoder and joystick.
	- If, after building your PasswordPump, you notice that the rotary encoder is
	  advancing through the alphabet when you turn the encoder counter-clockwise
		then you can reverse this behavior by selecting 'Lefty' in 
    Settings->Encoder Type.  This state survives power cycling but not factory
    reset.
  - If you wish to change the orientation of the display to the rotary encoder,
    (i.e. if you want to operate the encoder with your right hand) navigate to 
    Settings->Orientation.
  - See the Users Guide for more suggestions @ 
    https://github.com/seawarrior181/PasswordPump_II

  Contributors
  ============
  A lot of cargo programming was employed to build this program and Source code
  has been pulled from all over the internet, it would be impossible for me to 
  cite all contributors.

  Copyright
  =========
  - Copyright ©2018, ©2019, ©2020, @2021, ©2022, ©2023 Daniel J Murphy <dan-murphy@comcast.net>
  
  License                                                                       
  =======
  Creative Commons Attribution-NonCommercial-ShareAlike 4.0 International
  (CC BY-NC-SA 4.0). https://creativecommons.org/licenses/by-nc-sa/4.0/
  This program and device are distributed in the hope that they will be useful,
  but WITHOUT ANY WARRANTY; without even the implied warranty of MERCHANTABILITY
  or FITNESS FOR A PARTICULAR PURPOSE.

  You are free to:
    Share — copy and redistribute the material in any medium or format
    Adapt — remix, transform, and build upon the material
    The licensor cannot revoke these freedoms as long as you follow the license
    terms.

  Under the following terms:
  Attribution — You must give appropriate credit, provide a link to the license,
  and indicate if changes were made. You may do so in any reasonable manner, but
  not in any way that suggests the licensor endorses you or your use.

  NonCommercial — You may not use the material for commercial purposes.

  ShareAlike — If you remix, transform, or build upon the material, you must
  distribute your contributions under the same license as the original.

  No additional restrictions — You may not apply legal terms or technological 
  measures that legally restrict others from doing anything the license permits.

  Notices:
  You do not have to comply with the license for elements of the material in the
  public domain or where your use is permitted by an applicable exception or
  limitation.
  
  No warranties are given. The license may not give you all of the permissions
  necessary for your intended use. For example, other rights such as publicity,
  privacy, or moral rights may limit how you use the material.

  Libraries
  =========
	- https://github.com/LennartHennigs/Button2 				For the button on the 
																											rotary encoder 
	-	https://rweather.github.io/arduinolibs/index.html For encrypting 
																											credentials and for 
																											hashing the master 
																											password 
  - https://github.com/greiman/SSD1306Ascii           SSD1306Ascii is an 
                                                      unbuffered character only 
                                                      library for small OLED 
                                                      displays like the Adafruit
                                                      1.3" and 0.96" Monochrome 
                                                      displays.
	-	https://github.com/adafruit/Adafruit_SPIFlash			For FAT filesystems on 
																											SPI flash chips 
	- https://github.com/thijse/Arduino-CmdMessenger 		A messaging library for 
																											the Arduino and 
																											.NET/Mono platforms.
                                                      Somewhat buggy but 
                                                      appreciated nonetheless.

  Use the versions of these libraries supplied here: 
    https://github.com/seawarrior181/PasswordPump_II/tree/master/Libraries
    
  Library Modifications
  =====================
	-	Changed Adafruit_SSD1306::begin in Adafruit_SSD1306.cpp to suppress display
    of the Adafruit splash screen on the SSD1306 display.  See the instructions
    provided under "Fixing Adafruit_SSD1306" in the Users Manual. 
  - As per the Users Manual it's necessary to make an edit to the 
    Arduino-CmdMessenger library so that it will compile.  On line 492 of 
    ...\arduino\libraries\Arduino-CmdMessenger-master\CmdMessenger.cpp, change 

      return '\0';

        to

      char *str;
      *str = '\0';
      return str;

  Burning The Firmware    
  ====================    
	From the Arduino IDE:
		1) Under Tools do the following:  
			- Set the Board: "Adafruit ItsyBitsy M4 (SAMD51)".  
                    or "Adafruit ItsyBitsy M0".  
			- Cache: “Enabled”
			- CPU Speed: “120 MHz (standard)”
			- Optimize: “Small (-Os) (standard)”
			- Max QSPI: “50 MHz (standard)”
			- USB Stack: “Arduino”
			- Debug: “Off”
			- Identify the port associated with your PasswordPump after you've readied
			  it for upload by double clicking on the reset button on the bottom of 
			  the device, and noticing that the RGB LED fades on and off slowly, then 
			  set the port in Tools, (for example, under Windows substitute %% for 
			  your port number; Port: COM%% Adafruit ItsyBitsy M4 (SAMD51)).
			- Programmer: “Arduino as ISP”
		2) Select Sketch->Upload
		3) Verify that the upload was successful

	Using BOSSA (full coverage of this topic appears in the Users Guide)
    1a)ItsyBitsy M0
         C:\Users\YourUserName\AppData\Local\Arduino15\packages\arduino\tools\bossac\1.7.0-arduino3\bossac.exe -i -d --port=COM95 -U true -i -e -w -v C:\Temp\PasswordPump_v_2_0.ino.bin -R
    1b)ItsyBitsy M4
         C:\Users\YourUserName\AppData\Local\Arduino15\packages\arduino\tools\bossac\1.7.0-arduino3\bossac.exe -i -d --port=COM52 -U -i --offset=0x4000 -w -v C:\Temp\PasswordPump_v_2_0.ino.bin -R
      (substitute the correct user name and port numbers above)
		2) Verify that the upload was successful
    3) Note that the offset is 0x2000 for the ItsyBitsy M0.  Otherwise you risk
       bricking the MCU, in which case you will need to ship the unit back to 
       me for fixing or desolder the display and follow the instructions here: 
       https://learn.adafruit.com/how-to-program-samd-bootloaders.  See the 
       Users Guide for more information on this topic.

  Drivers
  =======
  - It might be necessary to install the following drivers: 
    https://github.com/adafruit/Adafruit_Windows_Drivers/releases
    https://github.com/adafruit/Adafruit_Windows_Drivers/releases/tag/2.4.0.0
  
  Other Artifacts                                                              
  ===============
  - Users Guide:            https://github.com/seawarrior181/PasswordPump_II/blob/master/Password%20Pump%20II%20Users%20Guide.pdf  
  - Source code repository: https://github.com/seawarrior181/PasswordPump_II 
  - Project web site:       https://www.5volts.org/
  - PasswordPump Store:     https://www.tindie.com/stores/passwordpump/
  - YouTube Video:          https://www.youtube.com/watch?v=f4Iukt5VDUo&t=33s

  Bill Of Materials
  =================
  - 1 AdaFruit ItsyBitsy (32-bit ARM®, SAMD51 Cortex®-M4F MCU)
       Data Sheet: http://ww1.microchip.com/downloads/en/DeviceDoc/60001507E.pdf
  - 2 MICROCHIP - 25LC512-I/P - 512K SPI™ Bus Serial EEPROM DIP8, one primary 
       one backup.
    2 IC DIP Sockets, 8 pins each
       Data Sheet: http://ww1.microchip.com/downloads/en/DeviceDoc/20005715A.pdf
  - 1 SSD1306 I2C LED display 128x32 pixels.
       Data Sheet: https://cdn-shop.adafruit.com/datasheets/SSD1306.pdf
                   https://www.vishay.com/docs/37894/oled128o032dlpp3n00000.pdf
  - 1 RGB LED
  - 1 Rotary Encoder
      -or-
  - 1 Joystick
  - 3 220ohm resistors
  - 1 plastic knob for rotary encoder
	- 1 custom PCB or breadboard

  Cost
  ====
  - 1 AdaFruit ItsyBitsy (32-bit ARM®, SAMD21 Cortex®-M0 MCU)         $15.30
  - 2 MICROCHIP - 25LC512-I/P - 512K SPI™ Bus Serial EEPROM DIP8        6.86
  - 1 SSD1306 I2C LED display 128x32 pixels.                            2.03
  - 1 Custom PCB                                                        1.50
  - 1 micro USB to USB cable 100cm                                      1.48
  - 1 Rotary Encoder                                                    0.46
      -or-
  - 1 Joystick                                                          0.81 (omitted)
  - 1 plastic knob for rotary encoder                                   0.11
  - 2 IC DIP Sockets, 8 pins each                                       0.10
  - Solder                                                              0.10
  - 1 RGB LED diffused 5mm                                              0.05
  - 3 220ohm resistors                                                  0.01
                                                                      ------
  - Total Parts                                                       $28.00
                                                                      ======
  + Labor for assembly, packaging & shipping
  
  Connections (rotary encoder version)
  ===========
  - ItsyBitsy M0/M4
    Number  Name              Connect To / Notes
    1       RS                reset button
    2       3V                25LC256 Prim Pin 3 & 25LC256 Secondary Pin 3 
    3       AREF              
    4       VHI               
    5       A0                
    6       A1                
    7       A2                
    8       A3                
    9       A4                220 Ohm resistor->RGB LED Pin 3
    10      A5                
    11      SCK               25LC256 Prim Pin 6 & 25LC256 Secondary Pin 6
    12      MO                25LC256 Prim Pin 5 & 25LC256 Secondary Pin 5
    13      MI                25LC256 Prim Pin 2 & 25LC256 Secondary Pin 2
    14      2                 
    15      En                
    16      swdio             
    17      swclk             
    18      3                 
    19      4                 
    20      RX                
    21      TX                
    22      SDA               SSD1306 SDA, 4.7k Ohm resistor->ItsyBitsy Pin 31
    23      SCL               SSD1306 SCL, 4.7k Ohm resistor->ItsyBitsy Pin 31
    24      5! (VHI Out)      220 Ohm resistor->RGB LED Pin 4
    25      7                 Rotary Encoder Pin 3
    26      9                 Rotary Encoder Pin 1
    27      10                25LC256 Secondary Pin 1 Chip Select
    28      11                25LC256 Primary   Pin 1 Chip Select
    29      12                Rotary Encoder Pin 4
    30      13                220 Ohm resistor->RGB LED Pin 1
    31      USB               SSD1306 VCC
    32      G                 RGB LED Pin 2, 25LC256 Prim & Secon Pin 4, SSD1306
                              Pin 1, Rotary Encoder Pins 2 & 5
    33      BAT               

  - 2 25LC512 (External EEprom)
    Tested Part: MICROCHIP - 25LC512-I/P - 512K SPI™ Bus Serial EEPROM DIP8

    25LC512 Primary
    Number Name                 ConnectTo        Note
    1       CS                  pin 28 ItsyBitsy  Chip Select Input
    2       SO                  pin 13 ItsyBitsy  MISO - Serial Data Output
    3       WP                  pin  2 ItsyBitsy  Write Protect
    4       Vss                 pin  2 ItsyBitsy  Ground
    5       SI                  pin 12 ItsyBitsy  MOSI - Serial Data Input
    6       SCK                 pin 11 ItsyBitsy  SCLK - Serial Clock Input
    7       HOLD                pin  2 ItsyBitsy  Hold Input
    8       Vcc                 pin  2 ItsyBitsy  Supply Voltage 
    
    25LC512 Secondary
    Number Name                 ConnectTo        Note
    1       CS                  pin 27 ItsyBitsy  Chip Select Input
    2       SO                  pin 13 ItsyBitsy  MISO - Serial Data Output
    3       WP                  pin  2 ItsyBitsy  Write Protect
    4       Vss                 pin  2 ItsyBitsy  Ground
    5       SI                  pin 12 ItsyBitsy  MOSI - Serial Data Input
    6       SCK                 pin 11 ItsyBitsy  SCLK - Serial Clock Input
    7       HOLD                pin  2 ItsyBitsy  Hold Input
    8       Vcc                 pin  2 ItsyBitsy  Supply Voltage 

  - Rotary Encoder
      1 2 3
    
      4   5
    1 ItsyBitsy Pin 26
    2 ItsyBitsy Pin 32
    3 ItsyBitsy Pin 25
    4 ItsyBitsy Pin 29
    5 ItsyBitsy Pin 32
    
    
  - SSD13306
    GND VCC SCL SDA
    1   2   3   4
    1 GND     ItsyBitsy Pin 32
    2 VCC     ItsyBitsy Pin 31
    3 SCL     ItsyBitsy Pin 23
    4 SDA     ItsyBitsy Pin 22
    
  - RGB LED
    1 Red     220 Ohm resistor->ItsyBitsy Pin 30
    2 Ground  ItsyBitsy Pin 32
    3 Green   220 Ohm resistor->ItsyBitsy Pin 9
    4 Blue    220 Ohm resistor->ItsyBitsy Pin 24

  RGB Colors and Meanings
  =======================
  Green                     Logged in
  Orange                    Backing up EEprom memory
  Alternating Blue and Red  Initializing EEprom
  Purple                    Sending creds, backing up to EEprom, editing with 
                            computer.
  Red                       Error backing up or initializing EEprom, failed 
                            login attempt(s).
  Yellow                    Error backing up or initializing EEprom
	Alternating								Not logged in
  
  Budgeting Memory
  ================
  Sketch uses ? bytes (15%) of program storage space on the M4. Maximum is 
  507904 bytes.  The sketch uses about 33% of program storage space on the 
  M0.

  Running the PC Client (PasswordPumpGUI)
  =====================
  The Python program that can manage credentials stored on the PasswordPump is 
  available here: https://github.com/seawarrior181/PasswordPump_II/blob/master/v2_0_9/PassPumpGUI/PassPumpGUI_v2_0.py
  See the Users Guide for information about setting up the PasswordPumpGUI.
    
  Menu Navigation
  ===============
  Master Password                  
  Find Favorite
  Find All Accounts
    [scroll through accounts list] 
      Send Password <RET>          
      Send User & Pass             
      Send URL
      Send User Name               
      Send Pass (no <RET>)
      Send Account                 
      Edit Credentials             
        Edit Account Name         
        Edit User Name            
        Edit Password             
        Edit URL                  
        Indicate Style      
          usr<RTN>pass<RTN>
          usr<TAB>pass<RTN>
          usr<TAB>pass<TAB,RTN>
        Assign Groups             
          Favorites
          Work
          Personal
          Home
          School
          Financial
          Mail
          Custom
        GeneratePassword          
        Save to Old Password
      Delete Credentials [confirm]
      Send Old Password
  Find By Group
    Favorites
      [same as under Find All Accounts]
    Work
      [same as under Find All Accounts]
    Personal
      [same as under Find All Accounts]
    Home
      [same as under Find All Accounts]
    School
      [same as under Find All Accounts]
    Financial
      [same as under Find All Accounts]
    Mail
      [same as under Find All Accounts]
    Custom
      [same as under Find All Accounts]
  Add Account                      
    Account Name                   
    Edit User Name                 
    Edit Password                  
    Indicate Style                 
      usr<RTN>pass<RTN>
      usr<TAB>pass<RTN>
      usr<TAB>pass<TAB,RTN>
    GeneratePasswrd                
  Logout & Lock                           
  Backup/Restore
    Backup EEprom [confirm]       
    Restore EEprm Backup [confirm]
  Settings
    Show Password ON/OFF            
    Decoy Password ON/OFF
    RGB LED Intensity
      High
      Medium
      Low
      Off
    Timeout Minutes
      30
      60
      90
      120
      240
      Never
      1
    Login Attempts
      3
      5
      10
      25
	  Rename Groups
			Edit Group 1
			Edit Group 2
			Edit Group 3
			Edit Group 4
			Edit Group 5
			Edit Group 6
			Edit Group 7
    Change Master Psswrd
    Keyboard Language
      Czech
      Danish
      Finnish
      French
      German
      Norwegian
      Spanish
      Swedish
      United Kingdom
      United States
    Encoder Type
      Normal
      Lefty
    Font
      Arial14
      Arial_bold_14
      Callibri10
      TimesNewRoman13
      Adafruit5x7
      font5x7
      lcd5x7
      Stang5x7
      System5x7
    Orientation
      Lefty
      Righty
    Keyboard ON/OFF            
    Gened Password Size
      8
      10
      16
      24
      31
    Inter Char Delay
      0
      10
      25
      100
      250
  Fix Corruption [confirm]
  Factory Reset [confirm]   

  Error Codes  TODO: add more error codes
  ===========
  000 - SSD1306 allocation failed (only visible via serial)
  001 - Error navigating Off On menu
  002 - Error navigating main menu
  003 - Error navigating edit credentials menu
  004 - Error navigating send credentials menu
  005 - Error navigating settings menu
  006 - Error showing credential values 
  007 - Unrecognized event
  008 - Invalid state when showing Off On menu
  009 - Invalid login attempt maximum
  010 - Out of space
  011 - Corruption found
  012 - Out of space during import
  013 - Failed to open file for import
  014 - Failed to mount FAT file system during import
  015 - Failed to initialize flash during import
  016 - Invalid RGB LED Intensity position
  017 - Invalid maximum login attempt count
  018 - Invalid logout timeout value
  019 - Invalid keyboard, show password or decoy password value
  020 - Account name keeps encrypting to 255 in first char during import
  021 - User name is too long on import
  022 - Password is too long on import
  023 - Web site is too long on import
  024 - Account name is too long on import
  025 - Invalid group specified
  026 - Invalid search group specified
  027 - Invalid group menu item specified
  028 - Invalid state during event singl click
  029 - Invalid state encountered during rotate counter clockwise event
  030 - Invalid state encountered during rotate clockwise event
  031 - Empty credentials found in linked list
  032 - Corrupt linked list
  033 - Corrupt linked list in FindAccountPos.
  034 - Failed to initialize flash during PasswordPump CSV file import
  035 - Group length is greater than one
  036 - Too many fields found in PasswordPump CVS file during import
  037 - Failed to open PasswordPump CVS file for import
  038 - Invalid position in file menu
  039 - Encrypted account name starts with 255, fixing...
  040 - Invalid position when returning to a find by group menu
  041 - Corrupt link list encountered while counting accounts
  042 - Invalid position when returning to settings menu
	043 - Invalid group number when customizing groups
  044 - Invalid category number when customizing groups from PasswordPumpGUI
  045 - Invalid keyboard language specified
  046 - Invalid encoder type specified
  047 - Invalid font specified
  048 - Invalid orientation specified
  049 - Invalid edit menu item when setting help
  050 - Invalid settings menu item when setting help
  051 - Infinite loop when searching for list head
  052 - Original head position not equal to found head position
  053 - Infinite loop when searching for list tail
  054 - Infinite loop when counting accounts
  055 - Invalid style specified
  056 - Invalid login attempt count
  057 - Unknown command from PasswordPumpGUI
  058 - Invalid generated password size
  059 - Invalid inter character pause size

  Finally, the Program 
  ==============================================================================
//- Includes/Defines                                                            */
//#define __SAMD51__                   			   		  												    // <-- set this. Turn this on for Adafruit ItsyBitsy M4. _SAMD21_ and _SAMD51_ are mutually exclusive.
#define __SAMD21__                 	 						  	  										  	  // <-- set this. Turn this on for Adafruit ItsyBitsy M0. _SAMD21_ and _SAMD51_ are mutually exclusive.
//#define __RP2040__
#define __SSD1306__                                                             // __SSD1306__ and __SH1107__ are mutually exclusive.  Pick one based on the size of the display.
//#define __SH1107__                                                            // __SSD1306__ and __SH1107__ are mutually exclusive.  Pick one based on the size of the display.
  
#define ENCODER_NORMAL            0                                             // don't change this.
#define ENCODER_LEFTY             1                                             // don't change this.
#define ENCODER_DEFAULT           ENCODER_NORMAL                                // <-- set this. Set the encoder type default based on how the encoder is behaving
#define MODEL_ENCODER             1                                             // don't change this
#define MODEL_JOYSTICK            0                                             // don't change this
#define MODEL                     MODEL_ENCODER                                 // <-- set this.  to determine if this is a model with a joystick (1, or MODEL_JOYSTICK) or a model with a rotary encoder (0, or MODEL_ENCODER).

#ifdef __SAMD51__
  #define F_CPU                   120000000UL                                   // don't change this. micro-controller clock speed, max clock speed of ItsyBitsy M4 is 120MHz (well, it can be over clocked...)
#endif
#ifdef __SAMD21__
  #define F_CPU                   48000000UL                                    // don't change this. micro-controller clock speed, max clock speed of ItsyBitsy M0 is 48MHz 
#endif
#ifdef __RP2040__
  #define F_CPU                   133000000UL                                   // don't change this. micro-controller clock speed, max clock speed of ItsyBitsy RP2040 is 133MHz
#endif

#define FIRMWARE_VERSION          "2.0.9.02"                                    // the version of the firmware, this program

//#define SLOW_SPI
#define DEBUG_ENABLED             0                                             // <-- set this to 1 if you want debug info written to serial out.
#define TEST_EEPROM               0                                             // <-- set this if you only want to test the eeprom.  Read the code first to understand what this does.

#include <avr/pgmspace.h>
#include <avr/interrupt.h>
#include <Wire.h>
#include <Button2.h>                                                            // https://github.com/LennartHennigs/Button2 for the button on the rotary encoder 
#include "Keyboard.h"                                                           // 
#include "CzechKeyboard.h"                                                      //      
#include "DanishKeyboard.h"                                                     // 
#include "FinnishKeyboard.h"                                                    // 
#include "FrenchKeyboard.h"                                                     // 
#include "GermanKeyboard.h"                                                     // 
#include "NorwegianKeyboard.h"                                                  // 
#include "SpanishKeyboard.h"                                                    // 
#include "SwedishKeyboard.h"                                                    // 
#include "UKKeyboard.h"                                                         // 
#include "USKeyboard.h"                                                         // The default.
#include <SHA256.h>                                                             // https://rweather.github.io/arduinolibs/index.html for hashing the master password 
#include <AES.h>                                                                // https://rweather.github.io/arduinolibs/index.html for encrypting credentials 
#ifdef __SSD1306__
  #include <SSD1306Ascii.h>                                                     // https://github.com/greiman/SSD1306Ascii
  #include <SSD1306AsciiWire.h>                                                 // https://github.com/greiman/SSD1306Ascii
#endif
#ifdef __SH1107__
  //#include <Adafruit_GFX.h>                                                   // https://github.com/adafruit/Adafruit-GFX-Library
  //#include <Adafruit_SH110X.h>                                                // https://github.com/adafruit/Adafruit_SH110x
  #include "lcdgfx.h"
  #include "lcdgfx_gui.h"
#endif
#include <Adafruit_SPIFlash.h>                                                  // https://github.com/adafruit/Adafruit_SPIFlash
#include <CmdMessenger.h>																												// https://github.com/thijse/Arduino-CmdMessenger 

//#include <stdio.h>                                                            // needed for CSV file program
//#include <locale.h>
#include <string.h>                                                             //  "     "       "       "
#include <stdlib.h>
#include <assert.h>

//- Macros
#define _BV(bit)                  (1 << (bit))
#define MAX(x, y) (((x) > (y)) ? (x) : (y))
#define MIN(x, y) (((x) < (y)) ? (x) : (y))
#define getLoginFailures          read_eeprom_byte(GET_ADDR_LOGIN_FAILURES)     // The number of login failures that have occurred since the last successful login.
#define getResetFlag              read_eeprom_byte(GET_ADDR_RESET_FLAG)
#define getShowPasswordsFlag      read_eeprom_byte(GET_ADDR_SHOW_PW)
#define getKeyboardFlag           read_eeprom_byte(GET_ADDR_KEYBOARD_FLAG)
#define getRGBLEDInt              read_eeprom_byte(GET_ADDR_RGB_LED_INT)
#define getLogoutTimeout          read_eeprom_byte(GET_ADDR_LOGOUT_TIMEOUT)
#define getKeyboardType           read_eeprom_byte(GET_ADDR_KEYBOARD_TYPE)
#define getEncoderType            read_eeprom_byte(GET_ADDR_ENCODER_TYPE)
#define getFont                   read_eeprom_byte(GET_ADDR_FONT)
#define getOrientation            read_eeprom_byte(GET_ADDR_ORIENTATION)
#define getLoginAttempts          read_eeprom_byte(GET_ADDR_LOGIN_ATTEM_NUM)    // The number of login attempts before we factory reset
#define getDecoyPWFlag            read_eeprom_byte(GET_ADDR_DECOY_PW)
#define getGroupStatus						read_eeprom_byte(GET_ADDR_CATEGORY_1)
#define getGenPasswordSize        read_eeprom_byte(GET_ADDR_GEN_PW_SIZE)
#define getInterCharPause         read_eeprom_byte(GET_ADDR_INTER_CHAR_PAUSE)

//#if defined(__SAMD51__) && defined(SERIAL_PORT_USBVIRTUAL)                    // Required for Serial on Zero based boards
//  #define Serial SERIAL_PORT_USBVIRTUAL
//#endif

//#define KEEPASS_CSV             "KPEXPORT.CSV"                                // this functionality was removed.
//#define KEEPASS_COLUMNS         5                                             // this functionality was removed.

//#define PP_CSV                  "PPEXPORT.CSV"                                // this functionality was removed.
//#define PP_COLUMNS              5                                             // this functionality was removed.

//#define CP_CSV                  "CPEXPORT.CSV"                                // this functionality was removed.
//#define CP_COLUMNS              4                                             // this functionality was removed.

//- Defines

#define BAUD_RATE                 115200                                        //  Baud rate for the Serial monitor, best for 16MHz (was 38400)

#define RED_PIN                   5                                             // Pin locations for the RGB LED, must be PWM capable 
#define BLUE_PIN                  13                                            //   "
#ifdef __SAMD51__
  #define GREEN_PIN               A4                                            //   "
  #define SET_OUT_PIN							A2
#endif
#ifdef __SAMD21__
  #define GREEN_PIN               A2                                            //   "
  #define SET_OUT_PIN							A4
#endif
#ifdef __RP2040__
  #define GREEN_PIN               A2                                            //   "
  #define SET_OUT_PIN							A4
#endif

#define RANDOM_PIN                A0                                            // this pin must float; it's used to generate the seed for the random number generator

#ifdef __SAMD21__
  #define UNUSED_PIN2             A4
#endif
#ifdef __SAMD51__
  #define UNUSED_PIN2             A2
#endif
#ifdef __RP2040__
  #define UNUSED_PIN2             A2
#endif
//#define UNUSED_PIN3             A3
//#define UNUSED_PIN4             A5
#define UNUSED_PIN5               2
#define UNUSED_PIN6               3
#define UNUSED_PIN7               4
#define UNUSED_PIN8               1                                             // TX
#define UNUSED_PIN9               0                                             // RX

#define NO_LED_LIB_CHAR_WIDTH_PIX 6                                             // when entering chars via rotary encoder, the amount to advance the cursor for each character already entered
#define FIXED_CHAR_SPACING        10                                            // when entering chars via rotary encoder, the fixed amount to advance the cursor

#define ONE_SECOND                1000UL                                        // in microseconds

#define INITIAL_MEMORY_STATE_CHAR -1                                            // 11111111 binary twos complement, -1 decimal, 0xFF hex.  When factory fresh all bytes in EEprom memory = 0xFF.  char is signed by default. byte is unsigned.
#define INITIAL_MEMORY_STATE_BYTE 0xFF                                          // 11111111 binary twos complement, -1 decimal, 0xFF hex.  When factory fresh all bytes in EEprom memory = 0xFF. 255 unsigned decimal.
#define NULL_TERM                 0x00                                          // The null terminator, NUL, ASCII 0, or '\0'                 
#define DEFAULT_STYLE_CHAR        0x31                                          // '1'

#define SPI_SS_PRIMARY            11                                            // chip select primary (copy source)  (SPI)
#define SPI_SS_SECONDARY          10                                            // chip select secondary (copy target)  (SPI)
#define SPI_MOSI                  MOSI                                          // mosi (SPI)
#define SPI_MISO                  MISO                                          // miso (SPI)
#define SPI_SCK                   SCK                                           // clock (SPI)
#define SPI_SPEED                 5000000UL                                     // 5MHz (max is 5MHz@3.3v)
#define SPI_MODE                  SPI_MODE3                                     // SPI_MODE3 = Clock Polarity=1, Clock Phase=1, Output Edge=falling, Data Capture=rising
                                                                                // SPI_MODE1,2 & 3 @100000hz not tried
#define SLAVE_PRIMARY_SELECT      digitalWrite(SPI_SS_PRIMARY, LOW);            // write the slave select pin low
#define SLAVE_PRIMARY_DESELECT    digitalWrite(SPI_SS_PRIMARY, HIGH);           // write the slave select pin high
#define SLAVE_SECONDARY_SELECT    digitalWrite(SPI_SS_SECONDARY, LOW);          // write the slave select pin low
#define SLAVE_SECONDARY_DESELECT  digitalWrite(SPI_SS_SECONDARY, HIGH);         // write the slave select pin high

// SPI Instruction Set -- from data sheet

#define EEPROM_READ               0b00000011                                    // read memory
#define EEPROM_WRITE              0b00000010                                    // write to memory
#define EEPROM_WREN               0b00000110                                    // write enable
#define EEPROM_RDSR               0b00000101                                    // read status register
                                                                                // EEPROM Status Register Bits -- from data sheet
                                                                                // Use these to parse status register
#define EEPROM_WRITE_IN_PROGRESS  0
#define EEPROM_WRITE_ENABLE_LATCH 1
#define EEPROM_BLOCK_PROTECT_0    2
#define EEPROM_BLOCK_PROTECT_1    3

#define RGB_LED_HIGH              254                                           // 255 = INITIAL_MEMORY_STATE_BYTE, so making this 254.
#define RGB_LED_MEDIUM            32                                            // 128 was too bright
#define RGB_LED_LOW               8                                             // 64 was too bright
#define RGB_LED_OFF               0
#define RGB_LED_DEFAULT           RGB_LED_MEDIUM

#define ATTEMPTS_3                3 
#define ATTEMPTS_5                5
#define ATTEMPTS_10               10
#define ATTEMPTS_25               25
#define ATTEMPTS_DEFAULT          ATTEMPTS_10

#define MAX_ITERATION_COUNT       104857

#define LOGOUT_WARNING            25000                                         // flash red/blue LED for 25 seconds before logout

//- Memory Layout

#define MAX_AVAIL_ADDR_25LC256    0x7FFF                                        // 32767 max address for 25LC256 (start at 0)
#define MAX_AVAIL_ADDR_25LC512    0xFFFF                                        // 65535 max address for 25LC512  
#define MAX_AVAIL_ADDR_25LC1024   0x1FFFF                                       // max address for 25LC1024
#define MIN_AVAIL_ADDR            0x0000                                        // 0 assuming we start at the very beginning of EEprom
#define MAX_AVAIL_ADDR            MAX_AVAIL_ADDR_25LC512                        // 32,767. 25LC256 = 256kbits capacity.
#define MEMORY_INITIALIZED_FLAG   0x0001                                        // signals if memory has been initialized correctly
#define EEPROM_BPP_25LC256        0x0040                                        // 64. can't exceed 255 (real page size is 64 for 25LC256)
#define EEPROM_BPP_25LC512        0x0080                                        // 128. can't exceed 255 (real page size is 128 for 25LC512)
#define EEPROM_BPP_25LC1024       0x0100                                        // 256
#define EEPROM_BYTES_PER_PAGE     EEPROM_BPP_25LC512                            // 
#define CREDS_ACCOM_25LC256       0x007E                                        // 126 (((0x7FFF + 1)/256)) - 1)  | (((MAX_AVAIL_ADDR_25LC256 + 1)/CREDS_TOT_SIZE)) - 2 for settings)
#define CREDS_ACCOM_25LC512       0x00FE                                        // 254 (((0xFFFF + 1)/256)) - 1)  | (((MAX_AVAIL_ADDR_25LC512 + 1)/CREDS_TOT_SIZE)) - 2 for settings)
#define CREDS_ACCOM_25LC1024      0x01FF                                        // 511
#define CREDS_ACCOMIDATED         (CREDS_ACCOM_25LC512 - 0x05)                  // -5 sets of creds for PyCmdMessenger defects = 249
#define DISPLAY_BUFFER_SIZE       21                                            // 0x0015, 21; room for 20 chars and the null terminator

#define WEBSITE_SIZE              0x0060                                        // 96 bytes
#define ACCOUNT_SIZE              0x0020                                        // 32 bytes
#define USERNAME_SIZE             0x0020                                        // 32 bytes
#define PASSWORD_SIZE             0x0020                                        // 32 bytes
#define OLD_PASSWORD_SIZE         0x0020                                        // 32 bytes (only used to calculate addresses, elsewhere we use PASSWORD_SIZE.
#define SALT_SIZE                 0x0010                                        // 16 bytes
#define STYLE_SIZE                0x0002                                        // 2 bytes, we are storing the null terminator
#define PREV_POS_SIZE             0x0001                                        // 1 byte, data type byte, no null terminator
#define NEXT_POS_SIZE             0x0001                                        // 1 byte, data type byte, no null terminator
#define GROUP_SIZE                0x0001                                        // 1 byte, designates the group to which the credential belongs
//------------------------------------------------------------------------------
#define CREDS_TOT_SIZE            0x0100                                        // 256 bytes (213 total, rounded up to 256. leaving an extra 43 bytes on the end so we're on the page boundary)
//==============================================================================// 32768 - 

                                                                                // Stored in first part of EEprom memory
#define GET_ADDR_WEBSITE(pos)     (MIN_AVAIL_ADDR + (pos * CREDS_TOT_SIZE))
#define GET_ADDR_ACCT(pos)        (MIN_AVAIL_ADDR + WEBSITE_SIZE + (pos * CREDS_TOT_SIZE))
#define GET_ADDR_USER(pos)        (MIN_AVAIL_ADDR + WEBSITE_SIZE + ACCOUNT_SIZE + (pos * CREDS_TOT_SIZE))
#define GET_ADDR_PASS(pos)        (MIN_AVAIL_ADDR + WEBSITE_SIZE + ACCOUNT_SIZE + USERNAME_SIZE + (pos * CREDS_TOT_SIZE))
#define GET_ADDR_OLD_PASS(pos)    (MIN_AVAIL_ADDR + WEBSITE_SIZE + ACCOUNT_SIZE + USERNAME_SIZE + PASSWORD_SIZE + (pos * CREDS_TOT_SIZE))
#define GET_ADDR_SALT(pos)        (MIN_AVAIL_ADDR + WEBSITE_SIZE + ACCOUNT_SIZE + USERNAME_SIZE + PASSWORD_SIZE + OLD_PASSWORD_SIZE + (pos * CREDS_TOT_SIZE))
#define GET_ADDR_STYLE(pos)       (MIN_AVAIL_ADDR + WEBSITE_SIZE + ACCOUNT_SIZE + USERNAME_SIZE + PASSWORD_SIZE + OLD_PASSWORD_SIZE + SALT_SIZE + (pos * CREDS_TOT_SIZE))
#define GET_ADDR_PREV_POS(pos)    (MIN_AVAIL_ADDR + WEBSITE_SIZE + ACCOUNT_SIZE + USERNAME_SIZE + PASSWORD_SIZE + OLD_PASSWORD_SIZE + SALT_SIZE + STYLE_SIZE + (pos * CREDS_TOT_SIZE))
#define GET_ADDR_NEXT_POS(pos)    (MIN_AVAIL_ADDR + WEBSITE_SIZE + ACCOUNT_SIZE + USERNAME_SIZE + PASSWORD_SIZE + OLD_PASSWORD_SIZE + SALT_SIZE + STYLE_SIZE + PREV_POS_SIZE + (pos * CREDS_TOT_SIZE)) 
#define GET_ADDR_GROUP(pos)       (MIN_AVAIL_ADDR + WEBSITE_SIZE + ACCOUNT_SIZE + USERNAME_SIZE + PASSWORD_SIZE + OLD_PASSWORD_SIZE + SALT_SIZE + STYLE_SIZE + PREV_POS_SIZE + NEXT_POS_SIZE + (pos * CREDS_TOT_SIZE)) // 100 @ pos==0
//                                (0              + 96           +           32 +            32 +            32 +                32 +        16 +          2 +             1 +             1 + (249 *            256)) =  63988 {Cannot exceed 65033}

#define MASTER_PASSWORD_SIZE      0x0010                                        // 16 bytes. aes256 keysize = 32 bytes.  aes128 keysize = 16 bytes, aes256 blocksize = 16!, only the first 15 chars are part of the password, the rest are ignored.
#define KEY_SIZE                  (MASTER_PASSWORD_SIZE + SALT_SIZE)            // 32 bytes, key size for AES-256 = 32 bytes
                                                                                // Stored in SETTINGS section of memory (last 256 bytes of EEprom)
#define RESET_FLAG_SIZE           0x0001                                        // 1 byte
#define LOGIN_FAILURES_SIZE       0x0001                                        // 1 byte
#define SHOW_PASSWORD_FLAG_SIZE   0x0001                                        // 1 byte
#define KEYBOARD_FLAG_SIZE        0x0001                                        // 1 byte
#define LIST_HEAD_SIZE            0x0001                                        // 1 byte Needs to be two bytes for 25LC512 and 25LC1024
#define MASTER_SALT_SIZE          0x0010                                        // 16 bytes
#define HASHED_MASTER_PASSWORD_SZ (MASTER_PASSWORD_SIZE + MASTER_SALT_SIZE)     // 32 the size of the hashed master password (store MASTER_SALT+MASTER_PASSWORD hashed)
#define RGB_LED_INTENSITY_SIZE    0x0001                                        // 1 byte
#define LOGOUT_TIMEOUT_SIZE       0x0001                                        // 1 byte
#define LOGIN_ATTEMPTS_NUM_SIZE   0x0001                                        // 1 byte
#define DECOY_PW_SIZE             0x0010                                        // 1 byte
#define CATEGORY_SIZE             0x000A																				// 10 bytes (there are 7 of these)
#define KEYBOARD_TYPE_SIZE        0x0001                                        // 1 byte
#define ENCODER_TYPE_SIZE         0X0001                                        // 1 byte
#define FONT_SIZE                 0x0001                                        // 1 byte, designates the desired font
#define ORIENTATION_SIZE          0x0001                                        // 1 byte, screen orientation, lefty (0) or righty (1)
#define GENERATED_PASSWORD_SIZE   0x0001                                        // 1 byte
#define INTER_CHAR_PAUSE_SIZE     0x0001                                        // 1 byte
//------------------------------------------------------------------------------
#define SETTINGS_TOTAL_SIZE       0x0100                                        // 256 (121 total, rounding up to 256)
//==============================================================================// 65536 - 256 = 65280/256 = 255 CREDS_ACCOMIDATED

#define GET_ADDR_SETTINGS         (MAX_AVAIL_ADDR - SETTINGS_TOTAL_SIZE)        // use the last page for storing the settings.
#define GET_ADDR_RESET_FLAG       (GET_ADDR_SETTINGS)                           // address of the reset flag; when not set to 0x01 indicates that memory hasn't been initialized; 32,767
#define GET_ADDR_LOGIN_FAILURES   (GET_ADDR_SETTINGS + RESET_FLAG_SIZE)         //
#define GET_ADDR_SHOW_PW          (GET_ADDR_SETTINGS + RESET_FLAG_SIZE + LOGIN_FAILURES_SIZE)     //
#define GET_ADDR_KEYBOARD_FLAG    (GET_ADDR_SETTINGS + RESET_FLAG_SIZE + LOGIN_FAILURES_SIZE + SHOW_PASSWORD_FLAG_SIZE) //
#define GET_ADDR_LIST_HEAD        (GET_ADDR_SETTINGS + RESET_FLAG_SIZE + LOGIN_FAILURES_SIZE + SHOW_PASSWORD_FLAG_SIZE + KEYBOARD_FLAG_SIZE) //  points to the head of the linked list
#define GET_ADDR_MASTER_SALT      (GET_ADDR_SETTINGS + RESET_FLAG_SIZE + LOGIN_FAILURES_SIZE + SHOW_PASSWORD_FLAG_SIZE + KEYBOARD_FLAG_SIZE + LIST_HEAD_SIZE) // location of the salt
#define GET_ADDR_MASTER_HASH      (GET_ADDR_SETTINGS + RESET_FLAG_SIZE + LOGIN_FAILURES_SIZE + SHOW_PASSWORD_FLAG_SIZE + KEYBOARD_FLAG_SIZE + LIST_HEAD_SIZE + MASTER_SALT_SIZE) // store hashed master password
#define GET_ADDR_RGB_LED_INT      (GET_ADDR_SETTINGS + RESET_FLAG_SIZE + LOGIN_FAILURES_SIZE + SHOW_PASSWORD_FLAG_SIZE + KEYBOARD_FLAG_SIZE + LIST_HEAD_SIZE + MASTER_SALT_SIZE + HASHED_MASTER_PASSWORD_SZ) // store setting for RGB LED intensity
#define GET_ADDR_LOGOUT_TIMEOUT   (GET_ADDR_SETTINGS + RESET_FLAG_SIZE + LOGIN_FAILURES_SIZE + SHOW_PASSWORD_FLAG_SIZE + KEYBOARD_FLAG_SIZE + LIST_HEAD_SIZE + MASTER_SALT_SIZE + HASHED_MASTER_PASSWORD_SZ + RGB_LED_INTENSITY_SIZE) // store the setting for the automatic logout timeout
#define GET_ADDR_LOGIN_ATTEM_NUM  (GET_ADDR_SETTINGS + RESET_FLAG_SIZE + LOGIN_FAILURES_SIZE + SHOW_PASSWORD_FLAG_SIZE + KEYBOARD_FLAG_SIZE + LIST_HEAD_SIZE + MASTER_SALT_SIZE + HASHED_MASTER_PASSWORD_SZ + RGB_LED_INTENSITY_SIZE + LOGOUT_TIMEOUT_SIZE) // store the setting for the EEProm part number
#define GET_ADDR_DECOY_PW         (GET_ADDR_SETTINGS + RESET_FLAG_SIZE + LOGIN_FAILURES_SIZE + SHOW_PASSWORD_FLAG_SIZE + KEYBOARD_FLAG_SIZE + LIST_HEAD_SIZE + MASTER_SALT_SIZE + HASHED_MASTER_PASSWORD_SZ + RGB_LED_INTENSITY_SIZE + LOGOUT_TIMEOUT_SIZE + LOGIN_ATTEMPTS_NUM_SIZE) // store the setting for the decoy password setting
#define GET_ADDR_KEYBOARD_TYPE    (GET_ADDR_SETTINGS + RESET_FLAG_SIZE + LOGIN_FAILURES_SIZE + SHOW_PASSWORD_FLAG_SIZE + KEYBOARD_FLAG_SIZE + LIST_HEAD_SIZE + MASTER_SALT_SIZE + HASHED_MASTER_PASSWORD_SZ + RGB_LED_INTENSITY_SIZE + LOGOUT_TIMEOUT_SIZE + LOGIN_ATTEMPTS_NUM_SIZE + DECOY_PW_SIZE) // store the setting for the keyboard type setting
#define GET_ADDR_ENCODER_TYPE     (GET_ADDR_SETTINGS + RESET_FLAG_SIZE + LOGIN_FAILURES_SIZE + SHOW_PASSWORD_FLAG_SIZE + KEYBOARD_FLAG_SIZE + LIST_HEAD_SIZE + MASTER_SALT_SIZE + HASHED_MASTER_PASSWORD_SZ + RGB_LED_INTENSITY_SIZE + LOGOUT_TIMEOUT_SIZE + LOGIN_ATTEMPTS_NUM_SIZE + DECOY_PW_SIZE + KEYBOARD_TYPE_SIZE) // store the setting for the keyboard type setting
#define GET_ADDR_FONT             (GET_ADDR_SETTINGS + RESET_FLAG_SIZE + LOGIN_FAILURES_SIZE + SHOW_PASSWORD_FLAG_SIZE + KEYBOARD_FLAG_SIZE + LIST_HEAD_SIZE + MASTER_SALT_SIZE + HASHED_MASTER_PASSWORD_SZ + RGB_LED_INTENSITY_SIZE + LOGOUT_TIMEOUT_SIZE + LOGIN_ATTEMPTS_NUM_SIZE + DECOY_PW_SIZE + KEYBOARD_TYPE_SIZE + ENCODER_TYPE_SIZE) // store the setting for the font setting
#define GET_ADDR_ORIENTATION      (GET_ADDR_SETTINGS + RESET_FLAG_SIZE + LOGIN_FAILURES_SIZE + SHOW_PASSWORD_FLAG_SIZE + KEYBOARD_FLAG_SIZE + LIST_HEAD_SIZE + MASTER_SALT_SIZE + HASHED_MASTER_PASSWORD_SZ + RGB_LED_INTENSITY_SIZE + LOGOUT_TIMEOUT_SIZE + LOGIN_ATTEMPTS_NUM_SIZE + DECOY_PW_SIZE + KEYBOARD_TYPE_SIZE + ENCODER_TYPE_SIZE + FONT_SIZE) // store the setting for the orientation setting
#define GET_ADDR_GEN_PW_SIZE      (GET_ADDR_SETTINGS + RESET_FLAG_SIZE + LOGIN_FAILURES_SIZE + SHOW_PASSWORD_FLAG_SIZE + KEYBOARD_FLAG_SIZE + LIST_HEAD_SIZE + MASTER_SALT_SIZE + HASHED_MASTER_PASSWORD_SZ + RGB_LED_INTENSITY_SIZE + LOGOUT_TIMEOUT_SIZE + LOGIN_ATTEMPTS_NUM_SIZE + DECOY_PW_SIZE + KEYBOARD_TYPE_SIZE + ENCODER_TYPE_SIZE + FONT_SIZE + ORIENTATION_SIZE) // store the setting for default password size
#define GET_ADDR_INTER_CHAR_PAUSE (GET_ADDR_SETTINGS + RESET_FLAG_SIZE + LOGIN_FAILURES_SIZE + SHOW_PASSWORD_FLAG_SIZE + KEYBOARD_FLAG_SIZE + LIST_HEAD_SIZE + MASTER_SALT_SIZE + HASHED_MASTER_PASSWORD_SZ + RGB_LED_INTENSITY_SIZE + LOGOUT_TIMEOUT_SIZE + LOGIN_ATTEMPTS_NUM_SIZE + DECOY_PW_SIZE + KEYBOARD_TYPE_SIZE + ENCODER_TYPE_SIZE + FONT_SIZE + ORIENTATION_SIZE + GENERATED_PASSWORD_SIZE) // store the setting inter character pause size
//                                (65279             +               1 +                   1 +                       1 +                  1 +              1 +               16 +                        32 +                      1 +                   1 +                       1 +             1 +                  1 +                 1 +         1 +                1 +                       1) = 65341

#define GET_ADDR_CATEGORY_1				(MAX_AVAIL_ADDR - (SETTINGS_TOTAL_SIZE * 2)) + (CATEGORY_SIZE * 1) // Should have started this at 0? place the categories on the second to last page on EEprom
#define GET_ADDR_CATEGORY_2				(MAX_AVAIL_ADDR - (SETTINGS_TOTAL_SIZE * 2)) + (CATEGORY_SIZE * 2) // 65033 - 65103
#define GET_ADDR_CATEGORY_3				(MAX_AVAIL_ADDR - (SETTINGS_TOTAL_SIZE * 2)) + (CATEGORY_SIZE * 3)
#define GET_ADDR_CATEGORY_4				(MAX_AVAIL_ADDR - (SETTINGS_TOTAL_SIZE * 2)) + (CATEGORY_SIZE * 4)
#define GET_ADDR_CATEGORY_5				(MAX_AVAIL_ADDR - (SETTINGS_TOTAL_SIZE * 2)) + (CATEGORY_SIZE * 5)
#define GET_ADDR_CATEGORY_6				(MAX_AVAIL_ADDR - (SETTINGS_TOTAL_SIZE * 2)) + (CATEGORY_SIZE * 6)
#define GET_ADDR_CATEGORY_7				(MAX_AVAIL_ADDR - (SETTINGS_TOTAL_SIZE * 2)) + (CATEGORY_SIZE * 7)
//                                (65535          - (256                 * 2)) + (10 *            1) = 65033
//                                (65535          - (256                 * 2)) + (10 *            7) = 65093

//          EEProm Memory Map
// Start    Stop    Size  Description
//     0 -  63988   63988 Credential Sets (43 empty bytes on the end of each set)
// 63988 -  65023    1034 Empty
// 65024 -  65032      10 Empty (start of page boundry) This is a mistake, should not be empty see line 1217
// 65033 -  65103      70 Custom Categories (10 bytes each)
// 65104 -  65278     174 Empty
// 65279 -  65535     256 Settings (1st 63 for settings, 202 empty bytes on the end of settings)

//- Events
                                                                                // Assumption here is that using #define instead of enum will save memory
#define EVENT_NONE                0                                             // used to switch of the previous event to avoid infinite looping
#define EVENT_SINGLE_CLICK        1                                             // a single click on the rotary encoder
#define EVENT_LONG_CLICK          4                                             // holding the button on the rotary encoder down for more than 1 second(?) (changed from default directly in the library)
#define EVENT_ROTATE_CW           7                                             // turning the rotary encoder clockwise
#define EVENT_ROTATE_CC           8                                             // turning the rotary encoder counter clockwise.
#define EVENT_SHOW_MAIN_MENU      9                                             // to show the main menu
#define EVENT_SHOW_EDIT_MENU      11                                            // to show the menu used for editing account name, user name and password (creds)
#define EVENT_RESET               12                                            // Factory Reset event
#define EVENT_LOGOUT              13                                            // logging out of the device
#define EVENT_BACKUP              14                                            // copying the content of the primary external EEprom to the backup EEprom
#define EVENT_RESTORE             15                                            // restore from the backup EEprom to the primary EEprom
//#define EVENT_BACKUP_TO_FILE    16                                            // send all credentials out through the keyboard for capture in a text editor
#define EVENT_FIX_CORRUPTION      17                                            // fix a corrupt linked list
#define EVENT_DELETE_ACCT         18                                            // delete an account
//#define EVENT_IMPORT_KEEPASS_CSV19                                            // import a csv KeePass file
#define EVENT_SHOW_SETTINGS_MENU  20                                            // to show the settings menu
#define EVENT_SHOW_LG_ATTEM_MENU  21                                            // to show the set login attempts menu
#define EVENT_SHOW_RGB_INT_MENU   22                                            // to show the set RGB LED intensity menu
#define EVENT_SHOW_LOG_TIME_MENU  23                                            // to show the set automatic logout time menu
#define EVENT_SHOW_OFF_ON_MENU    24                                            // to show the off/on menu
#define EVENT_SHOW_FIND_BY_GROUP  25
#define EVENT_CHANGE_MASTER       26
//#define EVENT_IMPORT_PP_CSV     27                                            // import a csv PasswordPump file
#define EVENT_SHOW_FILE_MENU      28
//#define EVENT_IMPORT_CP_CSV     29
#define EVENT_SEARCH_FAVORITES    30
#define EVENT_SHOW_FAVORITES_MENU 31
#define EVENT_SHOW_GROUP_DEF_MENU 32
#define EVENT_SHOW_KEYBOARD_MENU  33
#define EVENT_SHOW_ENCODER_MENU   34
#define EVENT_SHOW_FONT_MENU      35
#define EVENT_SHOW_ORIENT_MENU    36
#define EVENT_SHOW_GEN_PW_SZ_MENU 37
#define EVENT_SHOW_INT_CHAR_MENU  38
#define EVENT_WAKE                39
#define EVENT_SUSPEND             99                                            // event to set when you want to suspend processing, like after calling factory reset.
                                                                                // Not using an enum here to save memory.  
//- States                                                                      

#define STATE_ENTER_MASTER        1                                             // entering the master password
#define STATE_SHOW_MAIN_MENU      2                                             // showing the main menu                              
#define STATE_FIND_ACCOUNT        3                                             // searching for an account                           
#define STATE_EDIT_STYLE          4                                             // editing the style for sending user name and password
//#define STATE_EDIT_GROUPS       5                                             // assigning groups to credentials
#define STATE_EDIT_USERNAME       6                                             // entering the user name  
#define STATE_EDIT_PASSWORD       7                                             // entering the password                              
#define STATE_EDIT_WEBSITE        8
#define STATE_EDIT_CREDS_MENU     9                                             // showing the edit menu                              
#define STATE_EDIT_ACCOUNT        10                                            // entering the account name; if you change this also change it in PassPumpGUI.py                          
#define STATE_SEND_CREDS_MENU     11                                            // showing the menu that sends credentials via keyboard     
#define STATE_CONFIRM_BACK_EEPROM 12                                            // confirming an action                               
#define STATE_CONFIRM_RESTORE     13                                            // confirming restore from backup EEprom              
#define STATE_CONFIRM_FIX_CORRUPT 14                                            // confirming fix corruption function                 
#define STATE_CONFIRM_DEL_ACCT    15                                            // confirming account/credentials delete              
#define STATE_CONFIRM_RESET       16                                            // confirming factory reset                           
#define STATE_CONFIRM_IMP_KP_CSV  17                                            // confirming import KeePass csv file
#define STATE_MENU_SETTINGS       18                                            // in the settings menu
#define STATE_MENU_LOGIN_ATTEM    19                                            // setting the login attempts before factory reset menu
#define STATE_MENU_RGB_INTENSITY  20                                            // setting the RGB LED intensity menu
#define STATE_MENU_LOGOUT_TIMEOUT 21                                            // setting the logout timeout value menu
#define STATE_MENU_OFF_ON         22                                            // setting Off or On
#define STATE_MENU_GROUPS         23
#define STATE_KEY_ON_OFF_MENU     24
#define STATE_SHOW_PW_ON_OFF_MENU 25
#define STATE_DECOY_ON_OFF_MENU   26
#define STATE_SEARCH_FAVORITES    27
#define STATE_SEARCH_WORK         28
#define STATE_SEARCH_PERSONAL     29
#define STATE_SEARCH_HOME         30
#define STATE_SEARCH_SCHOOL       31
#define STATE_SEARCH_FINANCIAL    32
#define STATE_SEARCH_MAIL         33
#define STATE_SEARCH_CUSTOM       34
#define STATE_MENU_FIND_BY_GROUP  35                                            //
#define STATE_CHANGE_MASTER       36
#define STATE_CONFIRM_IMP_PP_CSV  37                                            // confirming import KeePass csv file
#define STATE_MENU_FILE           38
#define STATE_CONFIRM_IMP_CP_CSV  39
#define STATE_FEED_SERIAL_DATA    40
#define STATE_MENU_DEFINE_GROUPS	41
#define STATE_EDIT_GROUP_1				42
#define STATE_EDIT_GROUP_2				43
#define STATE_EDIT_GROUP_3				44
#define STATE_EDIT_GROUP_4				45
#define STATE_EDIT_GROUP_5				46
#define STATE_EDIT_GROUP_6				47
#define STATE_EDIT_GROUP_7				48
#define STATE_MENU_KEYBOARD       49
#define STATE_MENU_ENCODER        50
#define STATE_MENU_FONT           51
#define STATE_MENU_ORIENT         52
#define STATE_MENU_SHOW_GEN_PW_SZ 53
#define STATE_MENU_INT_CHAR_PAUSE 54

//- I2C Address

#define SSD1306_I2C_ADDR          0x3C                                          // Slave 128x64 OLED I2C address
#define SH1107_I2C_ADDR           0x3C                                          // Slave 128x128 OLED I2C address

#define LONG_CLICK_LENGTH         500                                           // milliseconds to hold down the rotary encoder button to trigger EVENT_LONG_CLICK
#define JOYSTICK_SPEED            250                                           // when the joystick is held in one position this is the speed with which the next EVENT_ROTATE event is fired, in milliseconds
#define UN_PW_DELAY               1000UL                                        // time in milliseconds to wait after sending user name before sending password
#define PW_RTN_DELAY              25UL                                          // time in milliseconds to wait after sending password before sending return
#define SHA_ITERATIONS            1                                             // number of times to hash the master password (won't work w/ more than 1 iteration)
#define KHZ_4000                  400000UL                                      // Speed (in Hz) for Wire transmissions in SSD1306 library calls.
#define KHZ_100                   10000UL                                       // Speed (in Hz) for Wire transmissions following SSD1306 library calls.
#define BLANK_SCREEN_DELAY        5                                             // Minutes to wait before making the display blank when Timeout Minutes is set to Never.

//- Menus (globals)

#define KBD_MENU_O_POS            10                                            // where to append "FF" or "N" on the "Keyboard O" menu item in settings
#define SH_PW_MENU_O_POS          15                                            // where to append "FF" or "N" on the  "Show Password O" menu item in settings
#define SH_DC_MENU_O_POS          16                                            // where to append "FF" or "N" on the "Decoy Password O" menu item in settings
#define MENU_SIZE                 14                                            // selections in the menu

#define MAIN_MENU_NUMBER          0
#define MAIN_MENU_ELEMENTS        11                                            // number of selections in the main menu

char * mainMenu[] =               {              
                                                 "Master Password",             // menu picks appear only on the top line
                                                 "Find Favorites",              // find favorite credentials
                                                 "Find All Accounts",           // after an account is found send user sendMenu 
                                                 "Find by Group",               // search accounts by a particular group
                                                 "Edit with Computer",          // edit credentials with the python UI
                                                 "Add Account",
                                                 "Logout & Lock",               // locks the user out until master password is re-entered
                                                 "Backup & Restore",            // Backup, Restore a backup 
                                                 "Settings",                    // navigate to the settings menu
                                                 "Fix Corruption",              // fix any corruption in the linked list
                                                 "Factory Reset"              };// factory reset; erases all credentials from memory

#define ENTER_MASTER_PASSWORD     0                                             // locations of the main menu items
#define FIND_FAVORITE             1
#define FIND_ACCOUNT              2
#define FIND_BY_GROUP             3
#define EDIT_VIA_COMPUTER         4
#define ADD_ACCOUNT               5
#define LOGOUT                    6
#define FILE_MENU_SEL             7
#define SETTINGS                  8
#define FIX_CORRUPT_LIST          9
#define FACTORY_RESET             10

uint8_t menuNumber = MAIN_MENU_NUMBER;                                          // holds the menu number of the currently displayed menu
uint8_t elements = MAIN_MENU_ELEMENTS;                                          // holds the number of selections in the currently displayed menu
char *currentMenu[MENU_SIZE];                                                   // holds the content of the currently displayed menu.  An array of 10 pointers to char.

#define SEND_MENU_NUMBER          1
#define SEND_MENU_ELEMENTS        9                                             // number of selections in the send credentials menu
const char * const sendMenu[] =   {              
                                                 "Send Password <RET>",         // send the password followed by a carriage return
                                                 "Send User & Password",        // send the user name then the password UN_PW_DELAY milliseconds later
                                                 "Send URL",                    // send the URL of the associated website
                                                 "Send User Name",              // send the user name
                                                 "Send Pass (no <RET>)",
                                                 "Send Account",                // send the account name
                                                 "Send Old Password",           // send the previous password
                                                 "Edit Credentials",            // sends user to enterMenu menu
                                                 "Delete Credentials",          // delete the account
                                                 ""                           };

#define SEND_PASSWORD             0                                             // locations of the send credentials menu items
#define SEND_USER_AND_PASSWORD    1                                             
#define SEND_WEBSITE              2
#define SEND_USERNAME             3
#define SEND_PASSWORD_NO_RET      4
#define SEND_ACCOUNT              5
#define SEND_OLD_PASSWORD         6
#define EDIT_ACCOUNT              7
#define DELETE_ACCOUNT            8

#define EDIT_MENU_NUMBER          2
#define EDIT_MENU_ELEMENTS        8                                             // the number of selections in the menu for editing credentials
const char * const enterMenu[] =  {              
                                                 "Edit Account Name",           // menu picks appear only on the top line
                                                 "Edit User Name",              // edit the user name
                                                 "Edit Password",               // edit the password
                                                 "Edit URL",                    // edit the website URL
                                                 "Indicate Style",              // 
                                                 "Assign Groups",               // 
                                                 "Generate Password",           // generate a 31 character UUID for the password
                                                 "Save to Old Password",        // save the current password to the old password
                                                 ""                           };

#define EDIT_ACCT_NAME            0                                             // locations of the edit credentials menu items
#define EDIT_USERNAME             1
#define EDIT_PASSWORD             2
#define EDIT_WEBSITE              3
#define EDIT_STYLE                4
#define EDIT_GROUPS               5
#define GENERATE_PASSWORD         6
#define SAVE_OLD_PASSWORD         7

#define SETTINGS_MENU_NUMBER      3
#define SETTINGS_MENU_ELEMENTS    14                                             // the number of selections in the menu for changing settings

char *settingsMenu[] =                {
                                                 "Show Password",               // determines if passwords are displayed or masked with asterisk
                                                 "Decoy Password",              // Determines if a decoy password can be entered to automatically factory reset the device
                                                 "RGB LED Intensity",           // Setting the RGB LED's intensity High, Medium, Low, Off
                                                 "Timeout Minutes",             // set the timeout for automatic logout in minutes
                                                 "Login Attempts",              // the number of login attempts allowed before a factory reset occurs
																								 "Rename Groups",								// allows the user to rename the group categories
                                                 "Change Master Pass",   				// Change the master password
                                                 "Keyboard Language",           // Change the keyboard language
                                                 "Encoder Type",                // Change the encoder type
                                                 "Font",                        // Change the font
                                                 "Orientation",                 // Change display orientation
                                                 "Keyboard",                    // flag that determines if the input by keyboard feature is on or off
                                                 "Generated Pass Len",          // determines the size of the generated password
                                                 "Inter Char Delay",            // set the delay between characters when sent
                                                 ""                           };

#define SETTINGS_SET_SHOW_PW      0
#define SETTINGS_SET_DECOY        1
#define SETTINGS_SET_RGB_INT      2
#define SETTINGS_SET_TIMEOUT      3
#define SETTINGS_SET_LOGIN_ATTEM  4
#define SETTINGS_GROUP_DEFINITION 5
#define SETTINGS_CHANGE_MASTER    6
#define SETTINGS_KEYBOARD_LANG    7
#define SETTINGS_ENCODER_TYPE     8
#define SETTINGS_FONT             9
#define SETTINGS_ORIENTATION      10
#define SETTINGS_SET_KEYBOARD     11                                            //
#define SETTINGS_GEN_PW_SIZE      12
#define SETTINGS_CHAR_DELAY       13

#define LOGOUT_TIMEOUT_MENU_NUMBER    4
#define LOGOUT_TIMEOUT_MENU_ELEMENTS  7
const char * const logoutTimeoutMenu[] = {       
                                                 "30",                          // 30 half hour
                                                 "60",                          // INITIAL_MEMORY_STATE_BYTE, one hour
                                                 "90",                          // 90 one and a half hours
                                                 "120",                         // 120 two hours
                                                 "240",                         // 240 four hours
                                                 "1",                           // 1 one minute
                                                 "Never",                       // 0 never times out
                                                 ""                           };
#define LOGOUT_TIMEOUT_30         0
#define LOGOUT_TIMEOUT_60         1                                             // default
#define LOGOUT_TIMEOUT_90         2
#define LOGOUT_TIMEOUT_120        3
#define LOGOUT_TIMEOUT_240        4
#define LOGOUT_TIMEOUT_1          5
#define LOGOUT_TIMEOUT_0          6

#define LOGOUT_TIMEOUT_VAL_30     30
#define LOGOUT_TIMEOUT_VAL_60     60                                            // default
#define LOGOUT_TIMEOUT_VAL_90     90
#define LOGOUT_TIMEOUT_VAL_120    120
#define LOGOUT_TIMEOUT_VAL_240    240
#define LOGOUT_TIMEOUT_VAL_1      1
#define LOGOUT_TIMEOUT_VAL_0      0
#define LOGOUT_TIMEOUT_DEFAULT    LOGOUT_TIMEOUT_VAL_60
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
void loop() {                                                                   // executes forever until reset button is pressed or power is interrupted
  encoderButton.loop();                                                         // polling for button press TODO: replace w/ interrupt
  #if MODEL == MODEL_JOYSTICK
    pollJoystick();                                                             // poll the joystick for any changes in status
  #else
    pollEncoder();                                                              // tried to use interrupts for the encoder but the results were inconsistent
  #endif
  ProcessEvent();                                                               // process any events that might have occurred.
}

void pollJoystick() {

  uint8_t joyButtonState1 = digitalRead(joystick1);
  uint8_t joyButtonState2 = digitalRead(joystick2); 
  uint8_t joyButtonState3 = digitalRead(joystick3);
  uint8_t joyButtonState4 = digitalRead(joystick4);

  if (joyButtonState1 != joyOldButtonState1)
  {
    joyStickSpeed = JOYSTICK_SPEED;                                             // set the joystick speed back to normal
    if (millis () - joyButtonTime1 >= joyDebounceTime)
    {
      joyButtonTime1 = millis();                                                // when we closed the switch
      joyOldButtonState1 = joyButtonState1;                                     // remember for next time
      if (joyButtonState1 == LOW) {
        event = EVENT_ROTATE_CW;
      }
    }
  } else {
    if (joyButtonState1 == LOW) {                                               // joystick is being held in one position
      if (millis() - joyButtonTime1 >= joyStickSpeed) {
        joyButtonTime1 = millis();
        if (joyStickSpeed > 100) joyStickSpeed -= 20;
        event = EVENT_ROTATE_CW;
      }
    }
  }

  if (joyButtonState2 != joyOldButtonState2)
  {
    joyStickSpeed = JOYSTICK_SPEED;                                             // set the joystick speed back to normal
    if (millis () - joyButtonTime2 >= joyDebounceTime)
    {
      joyButtonTime2 = millis();                                                // when we closed the switch
      joyOldButtonState2 = joyButtonState2;                                     // remember for next time
      if (joyButtonState2 == LOW) {
        event = EVENT_ROTATE_CW;
      }
    }
  } else {
    if (joyButtonState2 == LOW) {                                               // joystick is being held in one position
      if (millis() - joyButtonTime2 >= joyStickSpeed) {
        joyButtonTime2 = millis();
        if (joyStickSpeed > 100) joyStickSpeed -= 20;
        event = EVENT_ROTATE_CW;
      }
    }
  }

  if (joyButtonState3 != joyOldButtonState3)
  {
    joyStickSpeed = JOYSTICK_SPEED;                                             // set the joystick speed back to normal
    if (millis () - joyButtonTime3 >= joyDebounceTime)
    {
      joyButtonTime3 = millis();                                                // when we closed the switch
      joyOldButtonState3 = joyButtonState3;                                     // remember for next time
      if (joyButtonState3 == LOW) {
        event = EVENT_ROTATE_CC;
      }
    }
  } else {
    if (joyButtonState3 == LOW) {
      if (millis() - joyButtonTime3 >= joyStickSpeed) {
        joyButtonTime3 = millis();
        if (joyStickSpeed > 100) joyStickSpeed -= 20;
        event = EVENT_ROTATE_CC;
      }
    }
  }

  if (joyButtonState4 != joyOldButtonState4)
  {
    joyStickSpeed = JOYSTICK_SPEED;                                             // set the joystick speed back to normal
    if (millis () - joyButtonTime4 >= joyDebounceTime)
    {
      joyButtonTime4 = millis();                                                // when we closed the switch
      joyOldButtonState4 = joyButtonState4;                                     // remember for next time
      if (joyButtonState4 == LOW) {
        event = EVENT_ROTATE_CC;
      }
    }
  } else {
    if (joyButtonState4 == LOW) {
      if (millis() - joyButtonTime4 >= joyStickSpeed) {
        joyButtonTime4 = millis();
        if (joyStickSpeed > 100) joyStickSpeed -= 20;
        event = EVENT_ROTATE_CC;
      }
    }
  }
}

void pollEncoder() {
  change = 0;
  curModeA = digitalRead(rotaryPin1);                                           // compare the four possible states to figure out what has happened
  curModeB = digitalRead(rotaryPin2);                                           // then increment/decrement the current encoder's position
  if (curModeA != lastModeA) {
    if (curModeA == LOW) {
      if (curModeB == LOW) {
        encPos--;
      } else {
        encPos++;
      }
    } else {
      if (curModeB == LOW) {
        encPos++;
      } else {
        encPos--;
      }
    }
  }
  if (curModeB != lastModeB) {
    if (curModeB == LOW) {
      if (curModeA == LOW) {
        encPos++;
      } else {
        encPos--;
      }
    } else {
      if (curModeA == LOW) {
        encPos--;
      } else {
        encPos++;
      }
    }
  }
  lastModeA = curModeA;                                                         // set the current pin modes (HIGH/LOW) to be the last know pin modes
  lastModeB = curModeB;                                                         // for the next loop to compare to
  if (encPos < encPosLast) {                                                    // if this encoder's position changed, flag the change variable so we
    if (encPos%4 == 0) {                                                        // know about it later
      change = 1;
      event = EVENT_ROTATE_CW;
    }
  } else if (encPos > encPosLast) {
    if (encPos%4 == 0) {
      change = 1;
      event = EVENT_ROTATE_CC;
    }
  }
  
  if (change == 1) {
    encPosLast = encPos;                                                        // if an encoder has changed set encPosLast
  }
}

void ProcessEvent() {                                                           // processes events
  if (event != EVENT_NONE) {
    if (screenBlank) {                                                          // Added 2023-03-18 to prevent screen burn in. Any event turns screenBlank to false and the event is swallowed.
      screenBlank = false;                                                      // Added 2023-03-18 to prevent screen burn in.
      //event = EVENT_LONG_CLICK;												                        // I decided I don't like this behaviour.  2023-11-28
      event = EVENT_WAKE;														                            // Swallow the event.  2024-03-09
    }                                                                           // Added 2023-03-18 to prevent screen burn in. 
    DisableInterrupts();
    lastActivityTime = millis();                                                // bump up the lastActivityTime, we don't reset iterationCount here, not 
  } else {                                                                      // event == EVENT_NONE
    EnableInterrupts();
    if (++iterationCount == MAX_ITERATION_COUNT) {                              // we don't want to call millis() every single time through the loop
      milliseconds = millis();
      iterationCount = 0;                                                       // 
      if (logoutTimeout && authenticated) {                                     // if logoutTimeout != 0, i.e. there is a logout timeout set.
        unsigned long logoutTime = lastActivityTime +                           // logoutTimeout = 30, 60, 90, etc.; 
                         (logoutTimeout * MILLISECONDS_IN_A_MINUTE);            // convert logoutTimeout to milliseconds by multiplying by 1000 milliseconds in a second * 60 seconds in a minute.
        if (milliseconds < logoutTime) {                                        // check to see if the device has been idle for logoutTimeout milliseconds
																																								// Need to find a way to get the display to clear every time we display a new number...
          long timeLeft = logoutTime - milliseconds;                            // calculate time remaining until logout 
          timeLeft = timeLeft/MILLISECONDS_IN_A_SECOND;                         // convert timeLeft to seconds, max of 4 decimal places
          if (timeLeft != oldTimeLeft) { 
            if (milliseconds - lastActivityTime > MILLISECONDS_IN_A_MINUTE) {   // if we've been idle for more than a minute, show seconds left until logout
              oldTimeLeft = timeLeft;
              uint8_t roundHoursTillLogout   = timeLeft / SECONDS_IN_AN_HOUR;
              uint8_t roundMinutesTillLogout = (timeLeft - (roundHoursTillLogout * SECONDS_IN_AN_HOUR)) / SECONDS_IN_A_MINUTE;
              uint8_t roundSecondsTillLogout = ((timeLeft - (roundHoursTillLogout * SECONDS_IN_AN_HOUR)) - (roundMinutesTillLogout * SECONDS_IN_A_MINUTE));
              char sTimeTillLogout[21];
              sprintf(sTimeTillLogout, "Time Left:  %2u:%02u:%02u", roundHoursTillLogout, roundMinutesTillLogout, roundSecondsTillLogout);
              DisplayToHelp(sTimeTillLogout);
            }
          }
          if ((milliseconds + LOGOUT_WARNING) > logoutTime) {                   // Check to see if we are within 25 seconds of logging out
            if (RGBLEDIntensity) {
              uint8_t oldRGBLEDIntensity = RGBLEDIntensity;
              RGBLEDIntensity = RGB_LED_HIGH;
              setRed();
              delayNoBlock(100UL);                                              // Flash bright red to warn that we're going to be logging out
              RGBLEDIntensity = oldRGBLEDIntensity;
              setGreen();
             }
          }
          return;                                                               // not time to logout yet and event == EVENT_NONE, so just return.
        } else {
          //sendLockAndLogout();                                                // Uncomment if you want the computer screen to lock when auto logout of PasswordPump; Send LEFT GUI - l to computer          
          event = EVENT_LOGOUT;                                                 // otherwise we've been idle for more than logoutTimeout, logout.
																																								// do not return, continue processing in this function
        }
      } else {																																	// logout timeout is not enabled or we are already logged out
                                                                                // Following 5 loc added 2023-03-18 to save the OLED from burn in, i.e. if logoutTimeout is not set (== 0) then clear the screen after BLANK_SCREEN_DELAY minutes of inactivity.
        unsigned long clearScreenTime = lastActivityTime +                      
                         (BLANK_SCREEN_DELAY * MILLISECONDS_IN_A_MINUTE);       // convert minutes to milliseconds by multiplying by 60000 milliseconds in a minute.
        if (milliseconds > clearScreenTime) {                                   // check to see if the device has been idle for BLANK_SCREEN_DELAY minutes
#ifdef __SSD1306__
          oled.clear();                                                         // blank out the OLED screen to prevent burn in
#endif
#ifdef __SH1107__
          oled.clear();
#endif
          screenBlank = true;                                                   // Let ProcessEvent() know that the screen is blank when event != EVENT_NONE.
        }
        return;                                                                 // return to loop()       
      }
    } else {                                                                    // iterationCount is < 1048575
			if (iterationCount % 32768 == 0) {
				if (!authenticated && !loginFailures && RGBLEDIntensity != RGB_LED_OFF) {	
					angle += 1;															  														// if we are logged out and there are no login failures
					if (angle > 360) angle = 0;
					trueHSV(angle);																		  									// pulse the RGB LED
				}
			}
			return;                                                                   // not time to check millis() yet, just return
    }
  }

  //DebugMetric("Event: ",event);
  //DebugMetric("machineState: ",machineState);
  if        (event == EVENT_ROTATE_CW) {                                        // scroll forward through something depending on state...
    if ((STATE_SHOW_MAIN_MENU == machineState) &&
         authenticated                                                      ) { // this prevents navigation away from 'Enter Master Password' when not 
                                                                                // authenticated.
      if (position < MAIN_MENU_ELEMENTS - 1) {                                  // prevent scrolling past the last item on the menu
        position++;
        MenuDown(currentMenu);                                                  // move one position down the current menu
      }
    } else if ((STATE_ENTER_MASTER   == machineState  ) ||											// event == EVENT_ROTATE_CW
               (STATE_EDIT_ACCOUNT   == machineState  ) ||
//             (STATE_EDIT_STYLE     == machineState  ) ||
               (STATE_EDIT_USERNAME  == machineState  ) ||
               (STATE_EDIT_PASSWORD  == machineState  ) ||
               (STATE_EDIT_WEBSITE   == machineState  ) ||
               (STATE_CHANGE_MASTER  == machineState  )	||
							 (STATE_EDIT_GROUP_1	 == machineState	) ||
							 (STATE_EDIT_GROUP_2	 == machineState	) ||
							 (STATE_EDIT_GROUP_3	 == machineState	) ||
							 (STATE_EDIT_GROUP_4	 == machineState	) ||
							 (STATE_EDIT_GROUP_5	 == machineState	) ||
							 (STATE_EDIT_GROUP_6	 == machineState	) ||
							 (STATE_EDIT_GROUP_7	 == machineState	)) {
      if (position < (LEN_ALL_CHARS - 2)) {
        position++;
      }
      char charToPrint = allChars[position];                                    // TODO: eliminate this assignment / needless charToPrint variable
      ShowChar(charToPrint, enterPosition);
    } else if (STATE_SEND_CREDS_MENU == machineState){											    // event == EVENT_ROTATE_CW
      if (position < SEND_MENU_ELEMENTS - 1) {
        position++;
        MenuDown(currentMenu);
        setHelpOnSendCredsMenu(position);
      }
    } else if (STATE_EDIT_CREDS_MENU == machineState){											    // event == EVENT_ROTATE_CW
      if ((position < (EDIT_MENU_ELEMENTS - 1)) && (acctCount > 0)) {           // we'll only show the edit account options when there's at least one account
        position++;
        MenuDown(currentMenu);
        SwitchRotatePosition(position);
        setHelpOnEditCredsMenu(position);
      }
    } else if (STATE_MENU_FIND_BY_GROUP == machineState) {											// event == EVENT_ROTATE_CW
      if ((position < (GROUP_MENU_ELEMENTS - 1)) && (acctCount > 0)) {          // we'll only show the edit account options when there's at least one account
				DisplayToItem((char *) (groupMenu + (++position)));
      }
    } else if ((STATE_KEY_ON_OFF_MENU     == machineState) ||										// event == EVENT_ROTATE_CW
               (STATE_SHOW_PW_ON_OFF_MENU == machineState) ||
               (STATE_DECOY_ON_OFF_MENU   == machineState)) {
      position = !position;                                                     // flip from 0 to 1 or from 1 to 0
      ShowMenu(position, currentMenu);
    } else if (STATE_MENU_LOGIN_ATTEM     == machineState) {									  // event == EVENT_ROTATE_CW
      if (position < LOGIN_ATTEMPTS_MENU_ELEMENTS - 1) {                        
        position++;
        MenuDown(currentMenu);
      }
    } else if (STATE_MENU_KEYBOARD       == machineState) {									    // event == EVENT_ROTATE_CW
      if (position < KEYBOARD_MENU_ELEMENTS - 1) {                        
        position++;
        MenuDown(currentMenu);
      }
    } else if (STATE_MENU_ENCODER        == machineState) {									    // event == EVENT_ROTATE_CW
      if (position < ENCODER_MENU_ELEMENTS - 1) {                        
        position++;
        MenuDown(currentMenu);
      }
    } else if (STATE_MENU_FONT           == machineState) {									    // event == EVENT_ROTATE_CW
      if (position < FONT_MENU_ELEMENTS - 1) {                        
        position++;
        MenuDown(currentMenu);
      }
    } else if (STATE_MENU_ORIENT         == machineState) {									    // event == EVENT_ROTATE_CW
      if (position < ORIENT_MENU_ELEMENTS - 1) {                        
        position++;
        MenuDown(currentMenu);
      }
    } else if (STATE_MENU_SHOW_GEN_PW_SZ == machineState) {									    // event == EVENT_ROTATE_CW
      if (position < GEN_PW_SIZE_MENU_ELEMENTS - 1) {                        
        position++;
        MenuDown(currentMenu);
      }
    } else if (STATE_MENU_INT_CHAR_PAUSE == machineState) {									    // event == EVENT_ROTATE_CW
      if (position < CHAR_DELAY_MENU_ELEMENTS - 1) {                        
        position++;
        MenuDown(currentMenu);
      }
    } else if (STATE_MENU_RGB_INTENSITY  == machineState) {									    // event == EVENT_ROTATE_CW
      if (position < RGB_INTENSITY_MENU_ELEMENTS - 1) {                         
        position++;
        MenuDown(currentMenu);
      }
    } else if (STATE_MENU_LOGOUT_TIMEOUT == machineState) {									    // event == EVENT_ROTATE_CW
      if (position < LOGOUT_TIMEOUT_MENU_ELEMENTS - 1) {                        
        position++;
        MenuDown(currentMenu);
      }
    } else if (STATE_EDIT_STYLE  == machineState) {									            // event == EVENT_ROTATE_CW
      if (position < STYLE_MENU_ELEMENTS - 1) {                        
        position++;
        MenuDown(currentMenu);
      }
    } else if ((STATE_SEARCH_FAVORITES     == machineState) ||									// event == EVENT_ROTATE_CW
               (STATE_SEARCH_WORK          == machineState) ||
               (STATE_SEARCH_PERSONAL      == machineState) ||
               (STATE_SEARCH_HOME          == machineState) ||
               (STATE_SEARCH_SCHOOL        == machineState) ||
               (STATE_SEARCH_FINANCIAL     == machineState) ||
               (STATE_SEARCH_MAIL          == machineState) ||
               (STATE_SEARCH_CUSTOM        == machineState)) {     
      acctPosition = getNextPtr(acctPosition);
      while ( (acctPosition != INITIAL_MEMORY_STATE_BYTE) &&
             !(readGroupFromEEprom(acctPosition) & groupFilter) ) {
        //position = acctPosition;
        acctPosition = getNextPtr(acctPosition);
      }
      if (acctPosition != INITIAL_MEMORY_STATE_BYTE) {                          // we found a member of the group
        position = acctPosition;
        readAcctFromEEProm(position, accountName);
        DisplayToItem((char *) accountName);
      } else {                                                                  // we reached the end of the linked list
        acctPosition = position;                                                // set acctPosition back to the last account found belonging to the group
      }
      event = EVENT_NONE;
    } else if (STATE_FIND_ACCOUNT == machineState) {     											  // event == EVENT_ROTATE_CW
      uint8_t nextPos = getNextPtr(position);
      if (nextPos != INITIAL_MEMORY_STATE_BYTE) {
        position = nextPos;
      }
      acctPosition = position;
      readAcctFromEEProm(acctPosition, accountName);
      DisplayToItem((char *) accountName);
    } else if ((STATE_CONFIRM_BACK_EEPROM == machineState ) || 								  // event == EVENT_ROTATE_CW
               (STATE_CONFIRM_RESTORE     == machineState ) ||
               (STATE_CONFIRM_FIX_CORRUPT == machineState ) ||
               (STATE_CONFIRM_RESET       == machineState ) ||
               (STATE_CONFIRM_DEL_ACCT    == machineState ) ||
               (STATE_CONFIRM_IMP_KP_CSV  == machineState ) ||
               (STATE_CONFIRM_IMP_PP_CSV  == machineState ) ||
               (STATE_CONFIRM_IMP_CP_CSV  == machineState )) {
      position = !position;
      ShowChar(confirmChars[position], POS_Y_N_CONFIRM);
    } else if (STATE_MENU_SETTINGS == machineState) {											      // event == EVENT_ROTATE_CW
      if (position < SETTINGS_MENU_ELEMENTS - 1) {                              // prevent scrolling past the last item on the menu
        position++;
        MenuDown(currentMenu);                                                  // move one position down the current menu
        setHelpOnSettingsMenu(position);
      }
    } else if (STATE_MENU_FILE == machineState) {																// event == EVENT_ROTATE_CW
      if (position < FILE_MENU_ELEMENTS - 1) {                                  // prevent scrolling past the last item on the menu
        position++;
        MenuDown(currentMenu);                                                  // move one position down the current menu
      }
    } else if (STATE_MENU_GROUPS == machineState) {															// event == EVENT_ROTATE_CW
      if (position < GROUP_MENU_ELEMENTS - 1) {                                 // prevent scrolling past the last item on the menu
				DisplayToItem((char *) (groupMenu + (++position)));
      }
    } else if (STATE_MENU_DEFINE_GROUPS == machineState) {											// event == EVENT_ROTATE_CW
      if (position < GROUP_EDIT_MENU_ELEMENTS - 1) {                            // prevent scrolling past the last item on the menu
        position++;
        MenuDown(currentMenu);                                                  // move one position down the current menu
      }
		}
    event = EVENT_NONE;                                                         // to prevent infinite looping
    
  } else if (event == EVENT_ROTATE_CC) {                                        // scroll backward through something depending on state...
    if (STATE_SHOW_MAIN_MENU == machineState) {
      if (position > FIND_FAVORITE) {                                           // don't show the Master Password menu item after successful authentication
        position--;
        MenuUp(currentMenu);
      }
    } else if ((STATE_ENTER_MASTER  == machineState ) ||                    		// EVENT_ROTATE_CC
               (STATE_EDIT_ACCOUNT  == machineState ) ||
//             (STATE_EDIT_STYLE    == machineState ) ||
               (STATE_EDIT_USERNAME == machineState ) ||
               (STATE_EDIT_PASSWORD == machineState ) ||
               (STATE_EDIT_WEBSITE  == machineState ) ||
               (STATE_CHANGE_MASTER == machineState ) ||
							 (STATE_EDIT_GROUP_1 	== machineState	) ||
							 (STATE_EDIT_GROUP_2 	== machineState	) ||
							 (STATE_EDIT_GROUP_3 	== machineState	) ||
							 (STATE_EDIT_GROUP_4 	== machineState	) ||
							 (STATE_EDIT_GROUP_5 	== machineState	) ||
							 (STATE_EDIT_GROUP_6 	== machineState	) ||
							 (STATE_EDIT_GROUP_7 	== machineState	)) {
      if (position > 0) {
        position--;
      }
      char charToPrint = allChars[position];
      ShowChar(charToPrint, enterPosition);
    } else if (STATE_SEND_CREDS_MENU == machineState ){
      if (position > 0) {
        position--;
        MenuUp(currentMenu);
        setHelpOnSendCredsMenu(position);
      }
    } else if (STATE_EDIT_CREDS_MENU == machineState){
      if (position > 0) {
        position--;
        MenuUp(currentMenu);
        SwitchRotatePosition(position);
        setHelpOnEditCredsMenu(position);
      }
    } else if (STATE_MENU_FIND_BY_GROUP   == machineState) {                    // EVENT_ROTATE_CC
			if (position > 0) {
				DisplayToItem((char *) (groupMenu + (--position)));
			}
    } else if ((STATE_KEY_ON_OFF_MENU     == machineState) ||
               (STATE_SHOW_PW_ON_OFF_MENU == machineState) ||
               (STATE_DECOY_ON_OFF_MENU   == machineState)   ) {                // EVENT_ROTATE_CC
      position = !position;                                                     // flip from 0 to 1 or from 1 to 0
      ShowMenu(position, currentMenu);
    } else if ((STATE_MENU_LOGIN_ATTEM    == machineState) ||
               (STATE_MENU_RGB_INTENSITY  == machineState) ||
               (STATE_MENU_LOGOUT_TIMEOUT == machineState) ||
               (STATE_MENU_KEYBOARD       == machineState) ||
               (STATE_MENU_ENCODER        == machineState) ||
               (STATE_MENU_FONT           == machineState) ||
               (STATE_MENU_ORIENT         == machineState) ||
               (STATE_MENU_SHOW_GEN_PW_SZ == machineState) ||
               (STATE_MENU_INT_CHAR_PAUSE == machineState) ||
               (STATE_EDIT_STYLE          == machineState)) {                   // EVENT_ROTATE_CC
      if (position > 0) {
        position--;
        MenuUp(currentMenu);
      }
    } else if ((STATE_SEARCH_FAVORITES     == machineState) ||
               (STATE_SEARCH_WORK          == machineState) ||
               (STATE_SEARCH_PERSONAL      == machineState) ||
               (STATE_SEARCH_HOME          == machineState) ||
               (STATE_SEARCH_SCHOOL        == machineState) ||
               (STATE_SEARCH_FINANCIAL     == machineState) ||
               (STATE_SEARCH_MAIL          == machineState) ||
               (STATE_SEARCH_CUSTOM        == machineState)) {                  // EVENT_ROTATE_CC     
      acctPosition = getPrevPtr(acctPosition);
      while ( (acctPosition != INITIAL_MEMORY_STATE_BYTE) &&
             !(readGroupFromEEprom(acctPosition) & groupFilter) ) {             // 
        acctPosition = getPrevPtr(acctPosition);
      }
      if (acctPosition != INITIAL_MEMORY_STATE_BYTE) {                          // we found a favorite
        position = acctPosition;
        readAcctFromEEProm(position, accountName);
        DisplayToItem((char *) accountName);
      } else {                                                                  // we reached the beginning of the linked list
        acctPosition = position;                                                // set acctPosition back to the last known member of the group
      }
      event = EVENT_NONE;
    } else if (STATE_FIND_ACCOUNT == machineState) {                            // EVENT_ROTATE_CC
      uint8_t prevPos = getPrevPtr(position);
      if (prevPos != INITIAL_MEMORY_STATE_BYTE) {
        position = prevPos;
      }
      acctPosition = position;
      readAcctFromEEProm(acctPosition, accountName);
      DisplayToItem((char *) accountName);
    } else if ((STATE_CONFIRM_BACK_EEPROM == machineState ) || 
               (STATE_CONFIRM_RESTORE     == machineState ) ||
               (STATE_CONFIRM_FIX_CORRUPT == machineState ) ||
               (STATE_CONFIRM_RESET       == machineState ) ||
               (STATE_CONFIRM_DEL_ACCT    == machineState ) ||
               (STATE_CONFIRM_IMP_KP_CSV  == machineState ) ||
               (STATE_CONFIRM_IMP_PP_CSV  == machineState ) ||
               (STATE_CONFIRM_IMP_CP_CSV  == machineState )) {                  // EVENT_ROTATE_CC
      if (position == 1) {                                                      // roll through the two options, N and Y
        position = 0;
      } else {
        position = 1; 
      }
      ShowChar(confirmChars[position], POS_Y_N_CONFIRM);
    } else if (STATE_MENU_SETTINGS == machineState) {                           // EVENT_ROTATE_CC
      if (position > 0) {                                                       // 
        position--;
        MenuUp(currentMenu);
        setHelpOnSettingsMenu(position);
      }
    } else if (STATE_MENU_FILE == machineState) {                               // EVENT_ROTATE_CC
      if (position > 0) {
        position--;
        MenuUp(currentMenu);
      }
    } else if (STATE_MENU_GROUPS == machineState) {                             // EVENT_ROTATE_CC
			if (position > 0) {
				DisplayToItem((char *) (groupMenu + (--position)));
			}
    } else if (STATE_MENU_DEFINE_GROUPS == machineState) {
      if (position > 0) {                            														// prevent scrolling past the last item on the menu
        position--;
        MenuUp(currentMenu);              	                                    // move one position down the current menu
      }
    } 
    event = EVENT_NONE;
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
