seawarrior181/PasswordPump_II/v2_0_9/PasswordPump_v_2_0/UKKeyboard.h

/*
  UKKeyboard.h

  Adapted for the PasswordPump: Copyright (c) 2020, Daniel Murphy
  Copyright (c) 2015, Arduino LLC
  Original code (pre-library): Copyright (c) 2011, Peter Barrett

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
  You should have received a copy of the GNU Lesser General Public
  License along with this library; if not, write to the Free Software
  Foundation, Inc., 51 Franklin St, Fifth Floor, Boston, MA  02110-1301  USA
*/
#ifndef UK_KEYBOARD_h
#define UK_KEYBOARD_h
#include "KeyboardTop.h"

static const uint8_t  _hidReportDescriptorUK[47]  = {

                                                                                //  Keyboard
    0x05, 0x01,                                                                 // USAGE_PAGE (Generic Desktop)  // 47
    0x09, 0x06,                                                                 // USAGE (Keyboard)
    0xa1, 0x01,                                                                 // COLLECTION (Application)
    0x85, 0x02,                                                                 //   REPORT_ID (2)
    0x05, 0x07,                                                                 //   USAGE_PAGE (Keyboard)
                                                
  0x19, 0xe0,                                                                   //   USAGE_MINIMUM (Keyboard LeftControl)
    0x29, 0xe7,                                                                 //   USAGE_MAXIMUM (Keyboard Right GUI)
    0x15, 0x00,                                                                 //   LOGICAL_MINIMUM (0)
    0x25, 0x01,                                                                 //   LOGICAL_MAXIMUM (1)
    0x75, 0x01,                                                                 //   REPORT_SIZE (1)
                                                  
  0x95, 0x08,                                                                   //   REPORT_COUNT (8)
    0x81, 0x02,                                                                 //   INPUT (Data,Var,Abs)
    0x95, 0x01,                                                                 //   REPORT_COUNT (1)
    0x75, 0x08,                                                                 //   REPORT_SIZE (8)
    0x81, 0x03,                                                                 //   INPUT (Cnst,Var,Abs)
                                                  
  0x95, 0x06,                                                                   //   REPORT_COUNT (6)
    0x75, 0x08,                                                                 //   REPORT_SIZE (8)
    0x15, 0x00,                                                                 //   LOGICAL_MINIMUM (0)
    0x25, 0x73,                                                                 //   LOGICAL_MAXIMUM (115)
    0x05, 0x07,                                                                 //   USAGE_PAGE (Keyboard)
                                                  
  0x19, 0x00,                                                                   //   USAGE_MINIMUM (Reserved (no event indicated))
    0x29, 0x73,                                                                 //   USAGE_MAXIMUM (Keyboard Application)
    0x81, 0x00,                                                                 //   INPUT (Data,Ary,Abs)
    0xc0,                                                                       // END_COLLECTION
};
                                                                                //                ASCII #
static const uint8_t  _asciimapUK[128]  =
{
	0x00,                                                                         // NUL              0
	0x00,                                                                         // SOH
	0x00,                                                                         // STX
	0x00,                                                                         // ETX
	0x00,                                                                         // EOT
	0x00,                                                                         // ENQ
	0x00,                                                                         // ACK  
	0x00,                                                                         // BEL
	0x2a,			                                                                    // BS	Backspace
	0x2b,			                                                                    // TAB	Tab
	0x28,			                                                                    // LF	Enter         10
	0x00,                                                                         // VT 
	0x00,                                                                         // FF 
	0x00,                                                                         // CR 
	0x00,                                                                         // SO 
	0x00,                                                                         // SI 
	0x00,                                                                         // DEL              
	0x00,                                                                         // DC1
	0x00,                                                                         // DC2
	0x00,                                                                         // DC3
	0x00,                                                                         // DC4              20
	0x00,                                                                         // NAK
	0x00,                                                                         // SYN
	0x00,                                                                         // ETB
	0x00,                                                                         // CAN
	0x00,                                                                         // EM 
	0x00,                                                                         // SUB
	0x00,                                                                         // ESC
	0x00,                                                                         // FS 
	0x00,                                                                         // GS 
	0x00,                                                                         // RS               30
	0x00,                                                                         // US 
                                                             
	0x2c,		                                                                      //  ' '
	0x1e|SHIFT,	                                                                  // !
	0x1f|SHIFT,	                                                                  // "  switched w/ @ for UK
	0x35|SHIFT,                                                                   // # replaced by ~
	0x21|SHIFT,                                                                   // $
	0x22|SHIFT,                                                                   // %
	0x24|SHIFT,                                                                   // &
	0x34,                                                                         // '
	0x26|SHIFT,                                                                   // (                40
	0x27|SHIFT,                                                                   // )
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
	0x31|SHIFT,                                                                   // |
	0x30|SHIFT,                                                                   // }
	0x20|SHIFT,                                                                   // ~ swapped with # but should be ¬ instead
	0				                                                                      // DEL              127 (ASCII is 7 bit)
};                                                             
// ascii british pound £ = "156", which is the number of the letter or symbol "£" in ASCII table.                                                             
// page 53: https://www.usb.org/sites/default/files/hut1_12.pdf                                                             
#endif                                                                          // #ifndef UK_KEYBOARD_h
