seawarrior181/PasswordPump_II/v2_0_9/PasswordPump_v_2_0/Keyboard.cpp

/*
  Keyboard.cpp

  Adapted for the PasswordPump: Copyright (c) 2020, Daniel Murphy
  Copyright (c) 2015, Arduino LLC
  Original code (pre-library): Copyright (c) 2011, Peter Barrett

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
  You should have received a copy of the GNU Lesser General Public
  License along with this library; if not, write to the Free Software
  Foundation, Inc., 51 Franklin St, Fifth Floor, Boston, MA  02110-1301  USA
*/

#include "Keyboard.h"

#if defined(_USING_HID)

                                                                                //================================================================================
                                                                                //	Keyboard

uint8_t _hidReportDescriptor[47] ;
uint8_t _asciimap[128] ;

Keyboard_::Keyboard_(void) 
{
}

void Keyboard_::InitKeyboard(const uint8_t passedAsciimap[128], const uint8_t passedHidReportDescriptor[47])
{
   for(uint8_t loop = 0; loop < 128; loop++) {
      _asciimap[loop] = passedAsciimap[loop];
   }
   for(uint8_t loop = 0; loop < 47; loop++) {
      _hidReportDescriptor[loop] = passedHidReportDescriptor[loop];
   }
	static HIDSubDescriptor node(_hidReportDescriptor, sizeof(_hidReportDescriptor));
	HID().AppendDescriptor(&node);
}

void Keyboard_::begin(void)
{
}

void Keyboard_::end(void)
{
}

void Keyboard_::sendReport(KeyReport* keys)
{
	HID().SendReport(2,keys,sizeof(KeyReport));
}

//extern
//const uint8_t _asciimap[128] PROGMEM;

uint8_t USBPutChar(uint8_t c);

                                                                                // press() adds the specified key (printing, non-printing, or modifier)
                                                                                // to the persistent key report and sends the report.  Because of the way 
                                                                                // USB HID works, the host acts like the key remains pressed until we 
                                                                                // call release(), releaseAll(), or otherwise clear the report and resend.
size_t Keyboard_::press(uint8_t k) 
{
	uint8_t i;
	if (k >= 136) {			                                                          // it's a non-printing key (not a modifier)
		k = k - 136;
	} else if (k >= 128) {	                                                      // it's a modifier key
		_keyReport.modifiers |= (1<<(k-128));
		k = 0;
	} else {				                                                              // it's a printing key
    k = _asciimap[k];
		if (!k) {
			setWriteError();
			return 0;
		}
		if (k & 0x80) {						                                                  // it's a capital letter or other character reached with shift
			_keyReport.modifiers |= 0x02;	                                            // the left shift modifier
			k &= 0x7F;
		}
	}
	
                                                                                // Add k to the key report only if it's not already present
                                                                                // and if there is an empty slot.
	if (_keyReport.keys[0] != k && _keyReport.keys[1] != k && 
		_keyReport.keys[2] != k && _keyReport.keys[3] != k &&
		_keyReport.keys[4] != k && _keyReport.keys[5] != k) {
		
		for (i=0; i<6; i++) {
			if (_keyReport.keys[i] == 0x00) {
				_keyReport.keys[i] = k;
				break;
			}
		}
		if (i == 6) {
			setWriteError();
			return 0;
		}	
	}
	sendReport(&_keyReport);
	return 1;
}

                                                                                // release() takes the specified key out of the persistent key report and
                                                                                // sends the report.  This tells the OS the key is no longer pressed and that
                                                                                // it shouldn't be repeated any more.
size_t Keyboard_::release(uint8_t k) 
{
	uint8_t i;
	if (k >= 136) {			                                                          // it's a non-printing key (not a modifier)
		k = k - 136;
	} else if (k >= 128) {	                                                      // it's a modifier key
		_keyReport.modifiers &= ~(1<<(k-128));
		k = 0;
	} else {				                                                              // it's a printing key
  	k = _asciimap[k];
		if (!k) {
			return 0;
		}
		if (k & 0x80) {							                                                // it's a capital letter or other character reached with shift
			_keyReport.modifiers &= ~(0x02);	                                        // the left shift modifier
			k &= 0x7F;
		}
	}
	
                                                                                // Test the key report to see if k is present.  Clear it if it exists.
                                                                                // Check all positions in case the key is present more than once (which it shouldn't be)
	for (i=0; i<6; i++) {
		if (0 != k && _keyReport.keys[i] == k) {
			_keyReport.keys[i] = 0x00;
		}
	}

	sendReport(&_keyReport);
	return 1;
}

void Keyboard_::releaseAll(void)
{
	_keyReport.keys[0] = 0;
	_keyReport.keys[1] = 0;	
	_keyReport.keys[2] = 0;
	_keyReport.keys[3] = 0;	
	_keyReport.keys[4] = 0;
	_keyReport.keys[5] = 0;	
	_keyReport.modifiers = 0;
	sendReport(&_keyReport);
}

size_t Keyboard_::write(uint8_t c)
{
	uint8_t p = press(c);                                                         // Keydown
	release(c);                                                                   // Keyup
	return p;                                                                     // just return the result of press() since release() almost always returns 1
}

size_t Keyboard_::write(const uint8_t *buffer, size_t size) {
	size_t n = 0;
	while (size--) {
		if (*buffer != '\r') {
			if (write(*buffer)) {
			  n++;
			} else {
			  break;
			}
		}
		buffer++;
	}
	return n;
}

                                                                                //Keyboard_ Keyboard;

#endif
